elliotmartin92/hv_lock/accurate_models/back_edge_crop.png

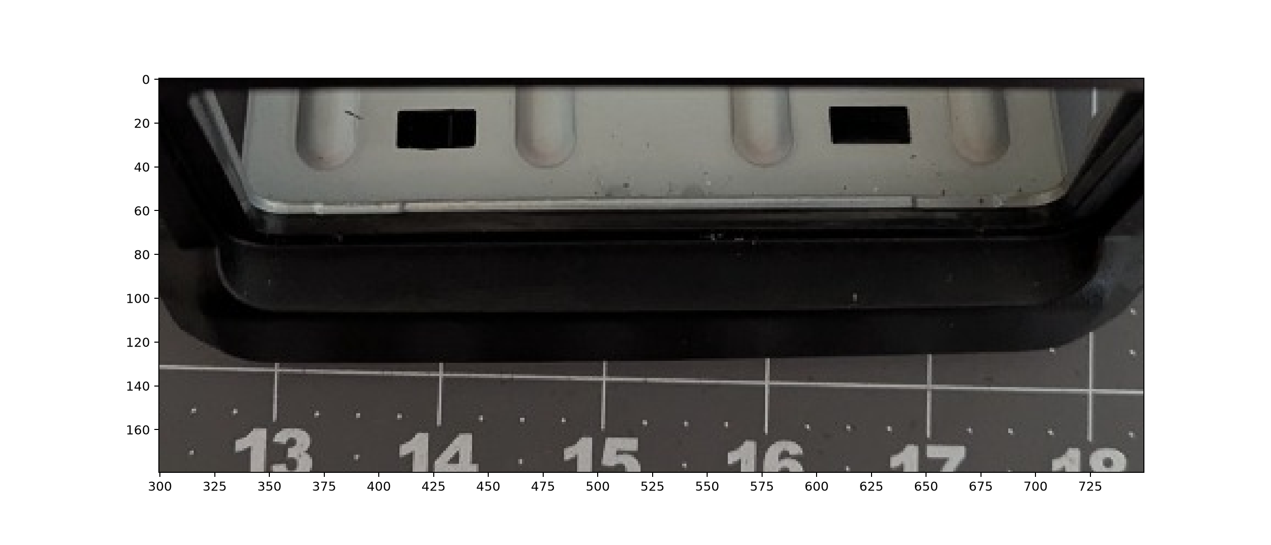
accurate_models/back_edge_crop.png
