elliotmartin92/hv_lock/accurate_models/cavity_floor_annotated.png

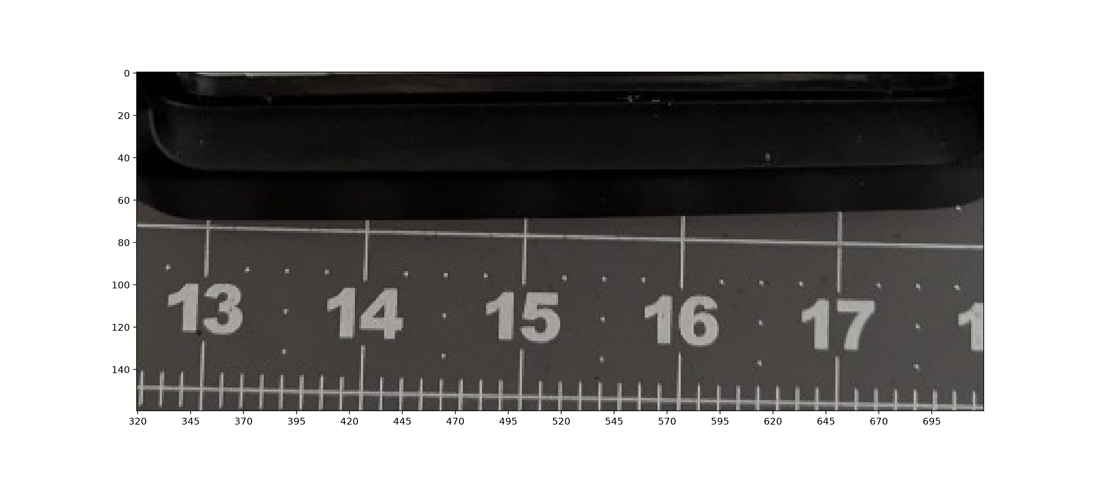
accurate_models/cavity_floor_annotated.png
