elliotmartin92/hv_lock/accurate_models/cavity_zoom.png

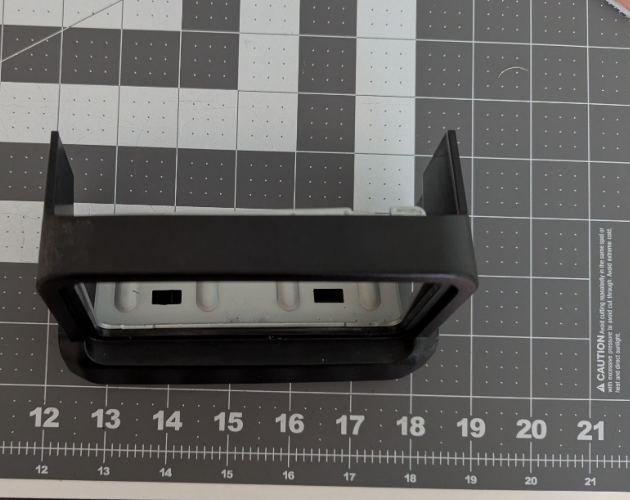
accurate_models/cavity_zoom.png
