elliotmartin92/hv_lock/accurate_models/connector_blueprint.png

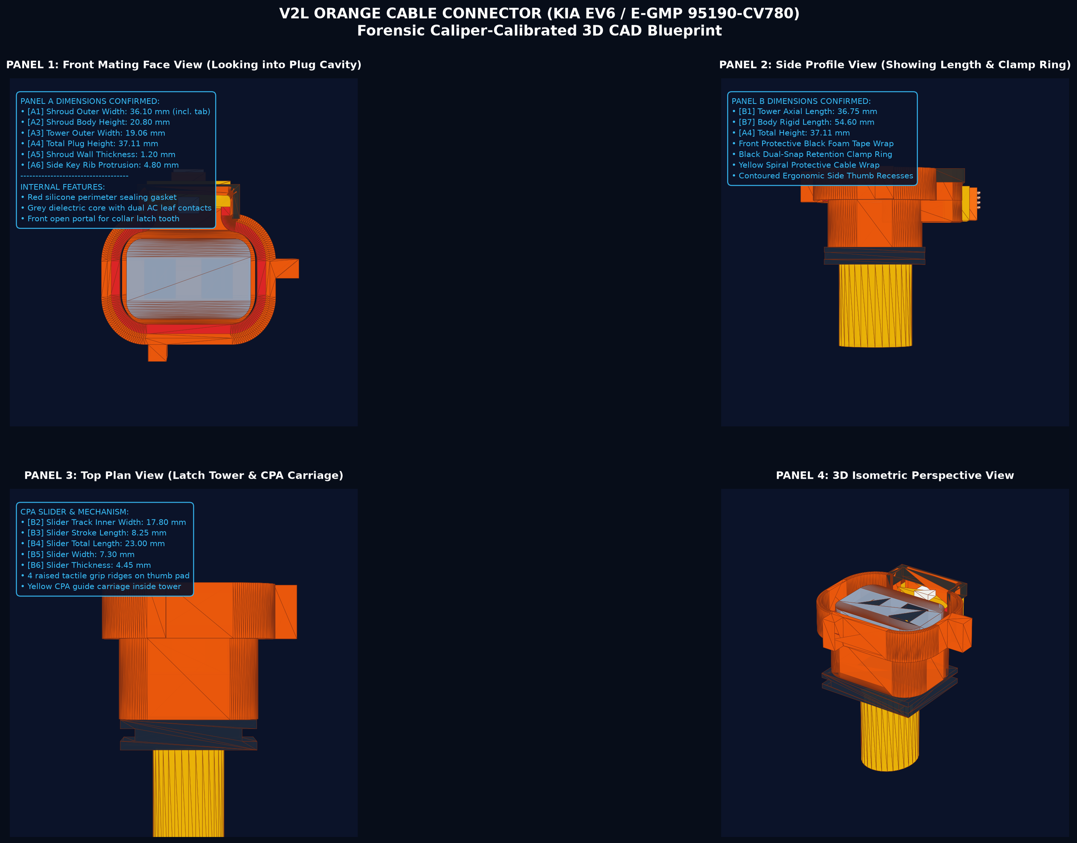
accurate_models/connector_blueprint.png
