elliotmartin92/hv_lock/accurate_models/find_round_holes.png

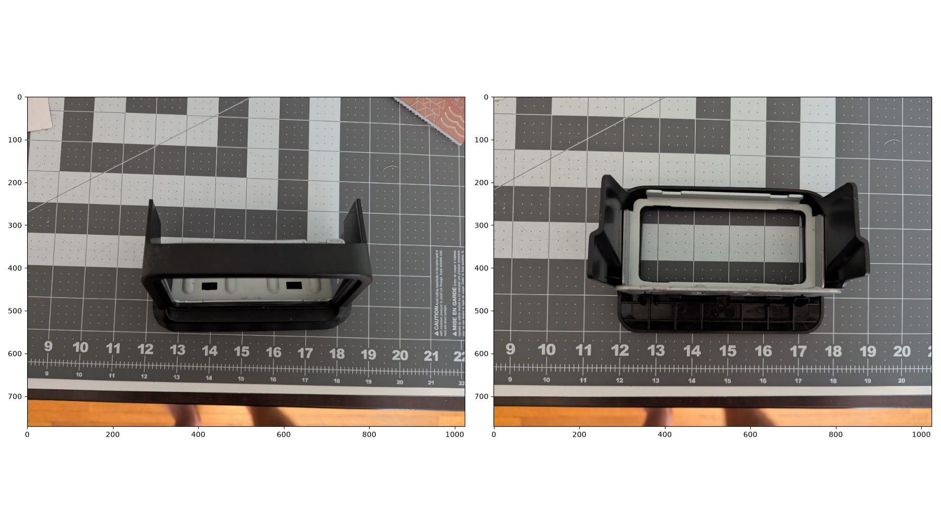
accurate_models/find_round_holes.png
