elliotmartin92/hv_lock/accurate_models/h7_clarification.png

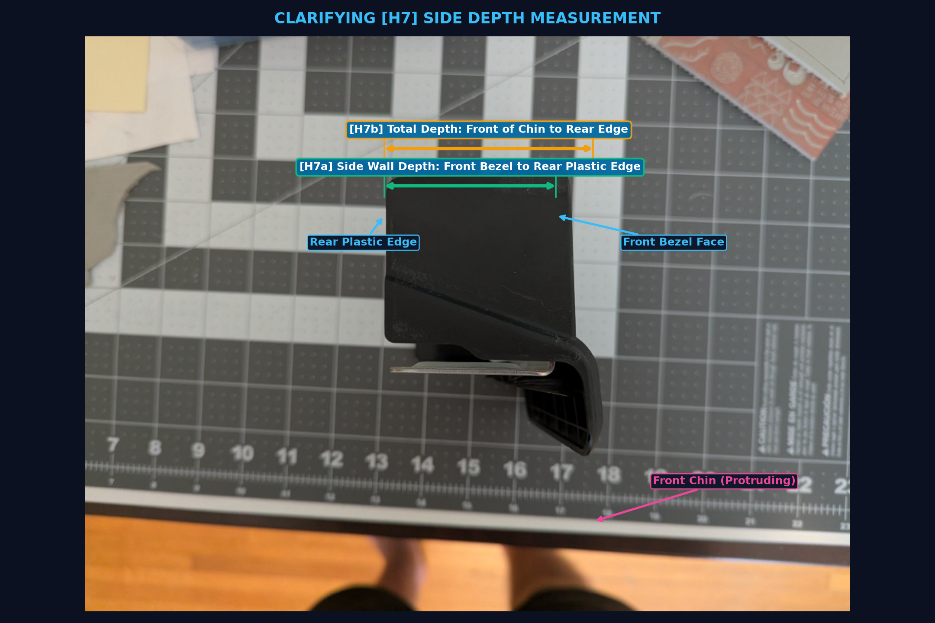
accurate_models/h7_clarification.png
