elliotmartin92/hv_lock/accurate_models/holes_crop.png

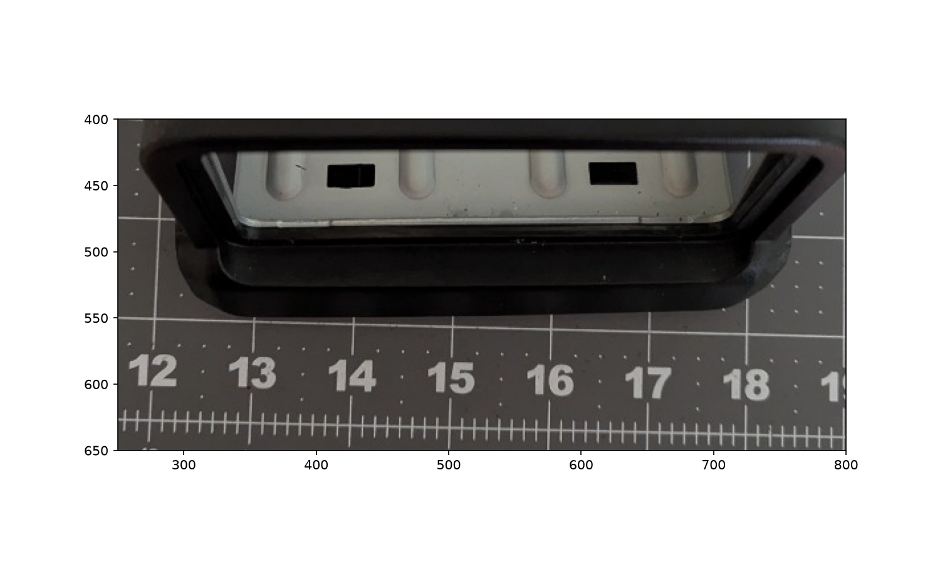
accurate_models/holes_crop.png
