elliotmartin92/hv_lock/accurate_models/holes_zoom.png

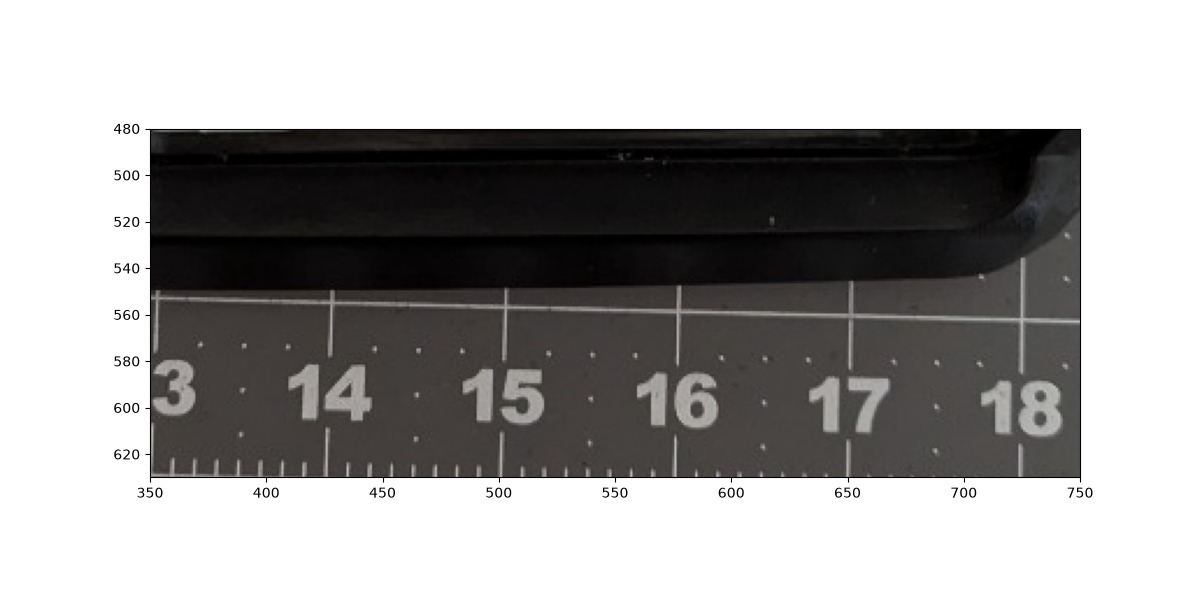
accurate_models/holes_zoom.png
