elliotmartin92/hv_lock/accurate_models/left_vs_right_check.png

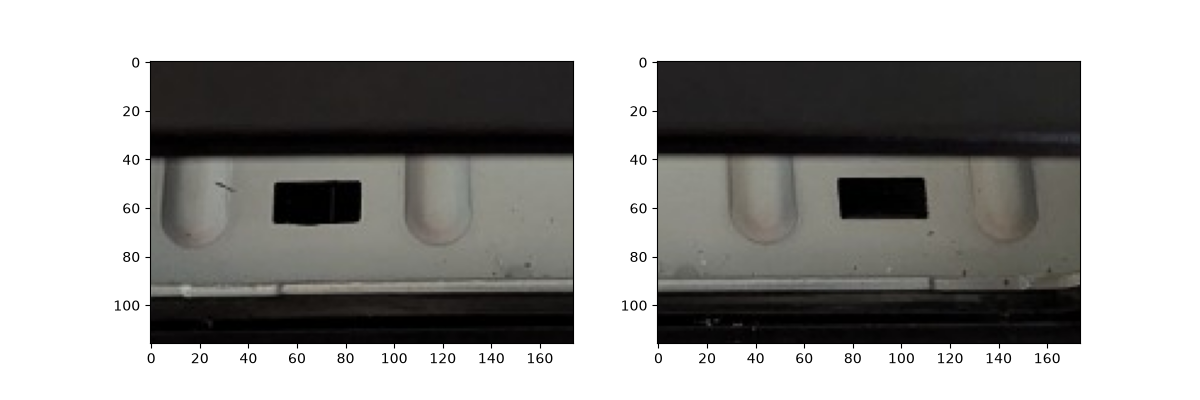
accurate_models/left_vs_right_check.png
