elliotmartin92/hv_lock/accurate_models/outer_housing_blueprint.png

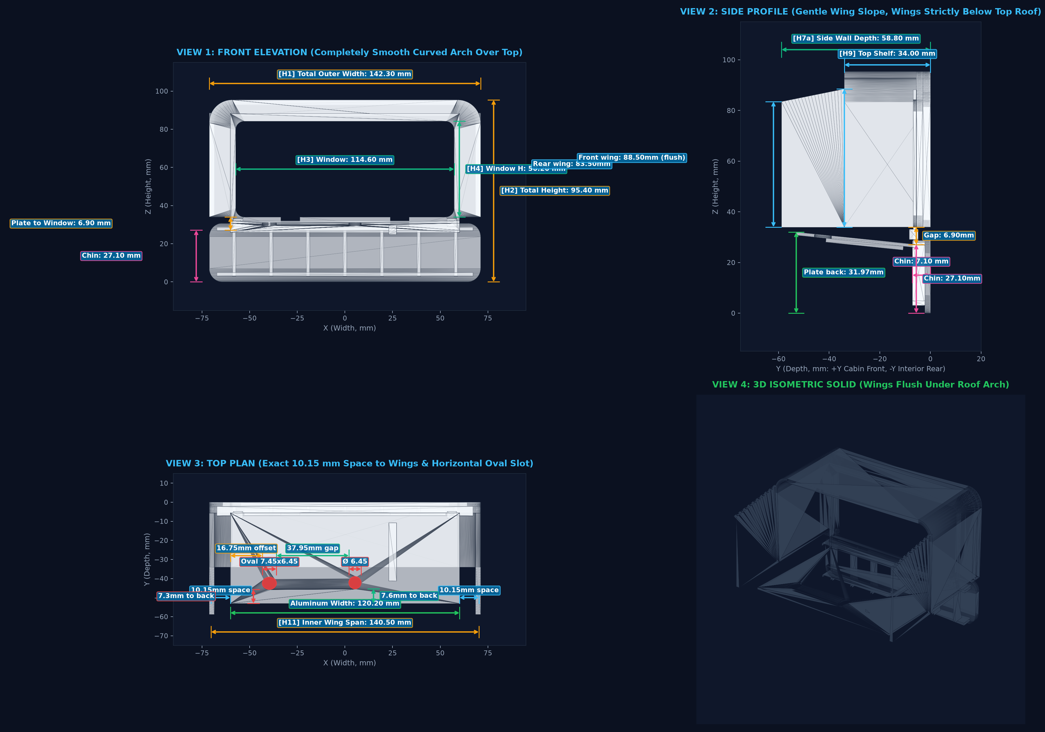
accurate_models/outer_housing_blueprint.png
