elliotmartin92/hv_lock/accurate_models/outlet_box_blueprint.png

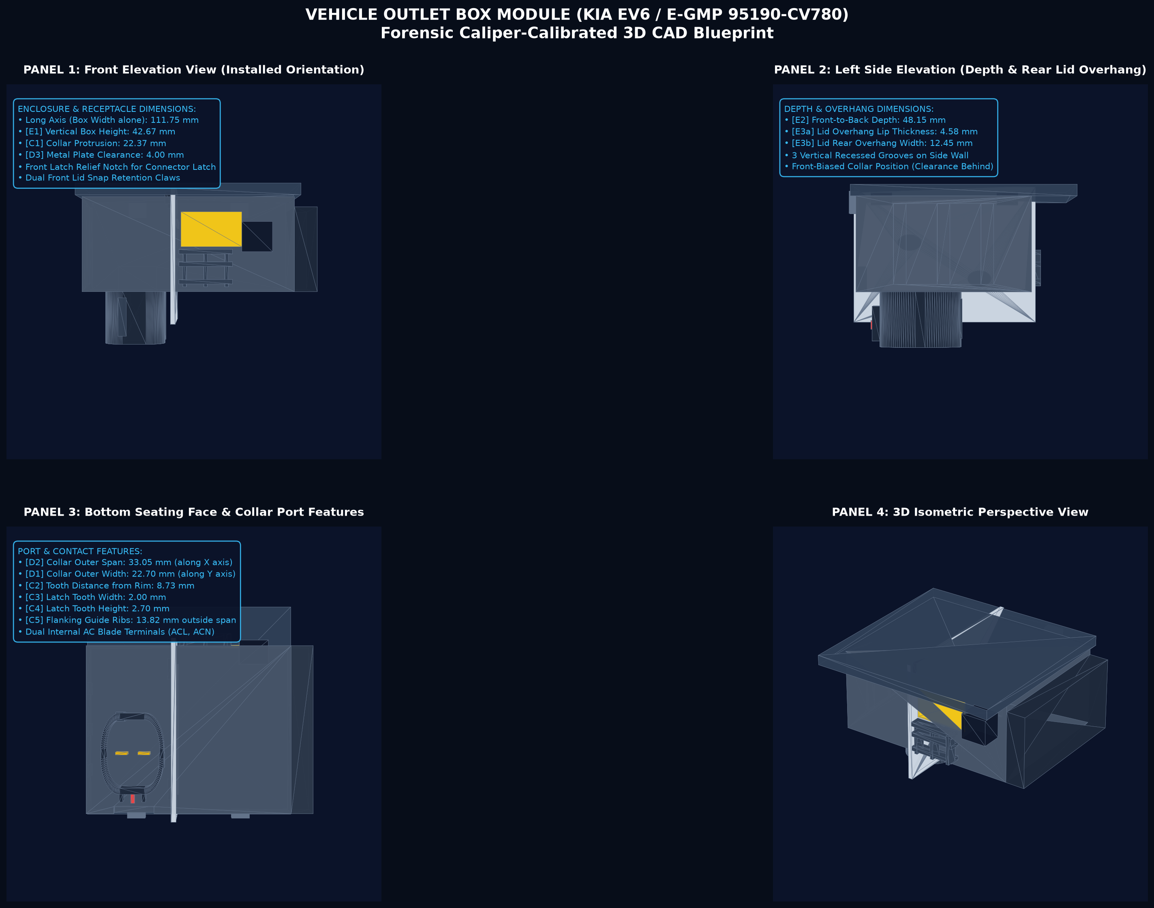
accurate_models/outlet_box_blueprint.png
