elliotmartin92/hv_lock/accurate_models/photo1_zoom.png

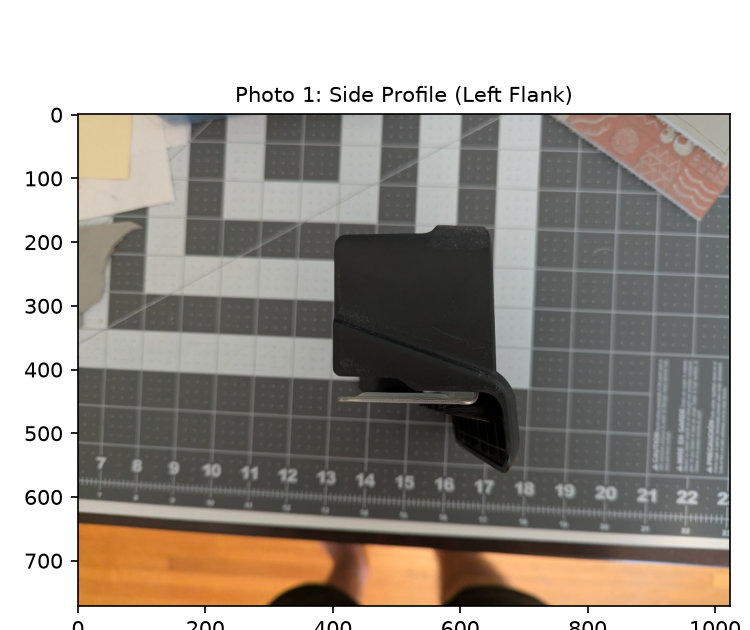
accurate_models/photo1_zoom.png
