elliotmartin92/hv_lock/accurate_models/photo3_zoom.png

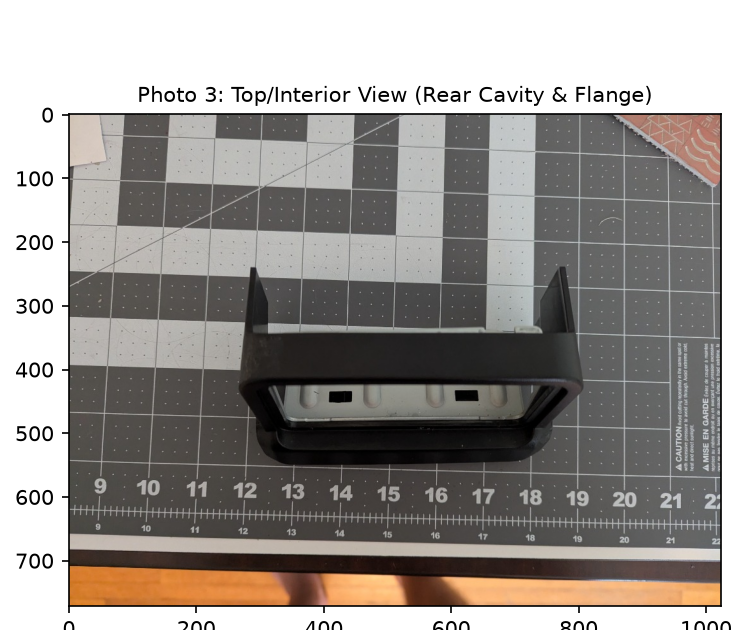
accurate_models/photo3_zoom.png
