elliotmartin92/hv_lock/accurate_models/photo5_zoom.png

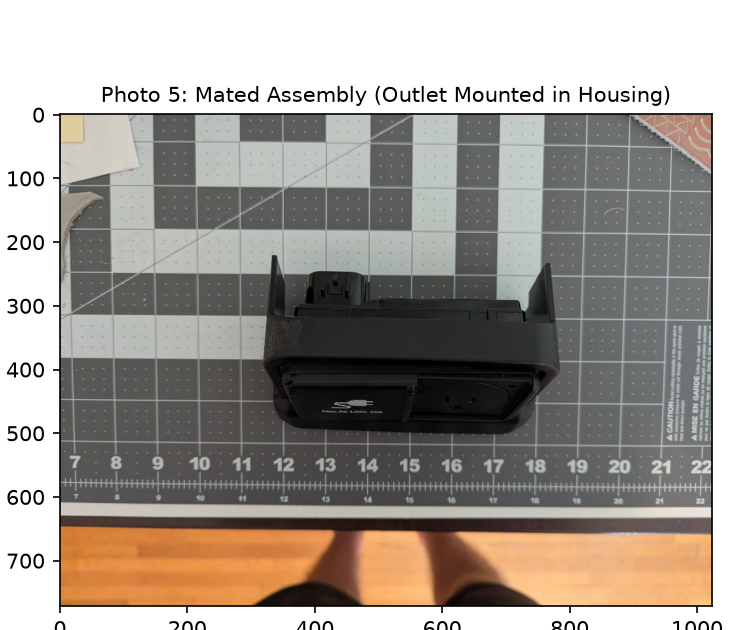
accurate_models/photo5_zoom.png
