elliotmartin92/hv_lock/accurate_models/plate_angle_lines.png

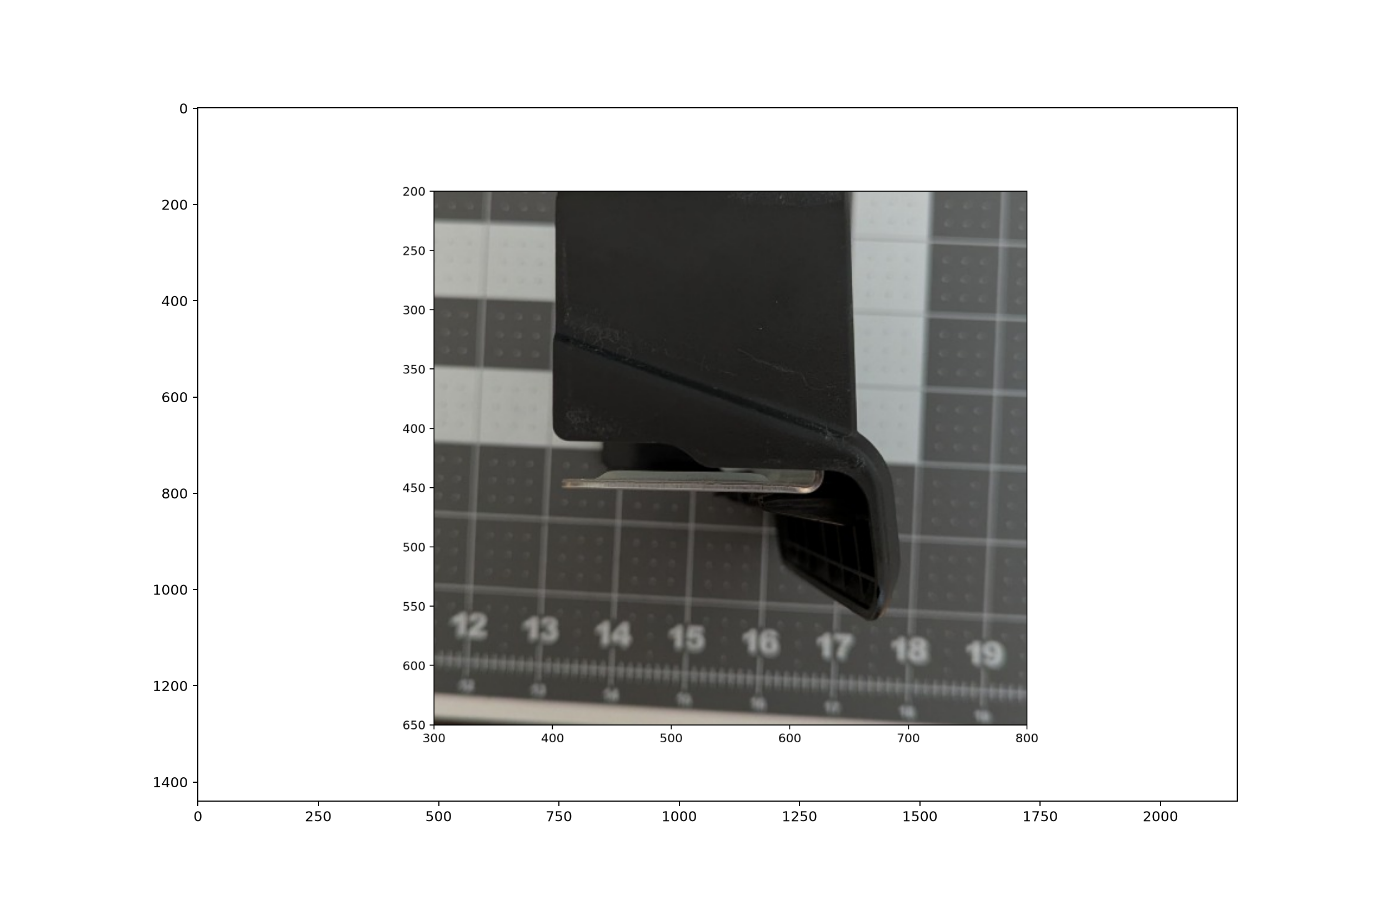
accurate_models/plate_angle_lines.png
