elliotmartin92/hv_lock/accurate_models/plate_angle_study.png

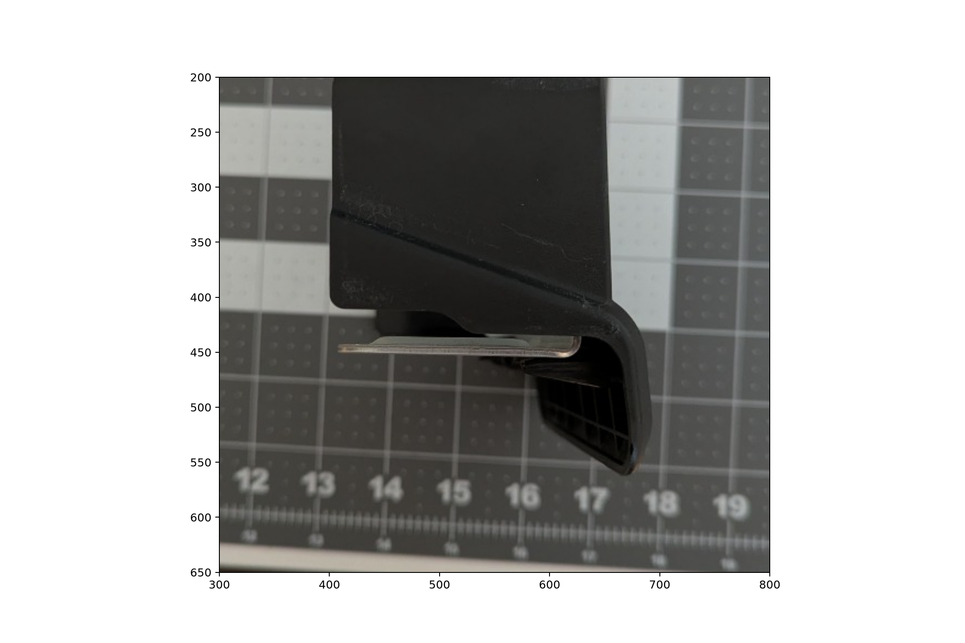
accurate_models/plate_angle_study.png
