elliotmartin92/hv_lock/accurate_models/profile_study.png

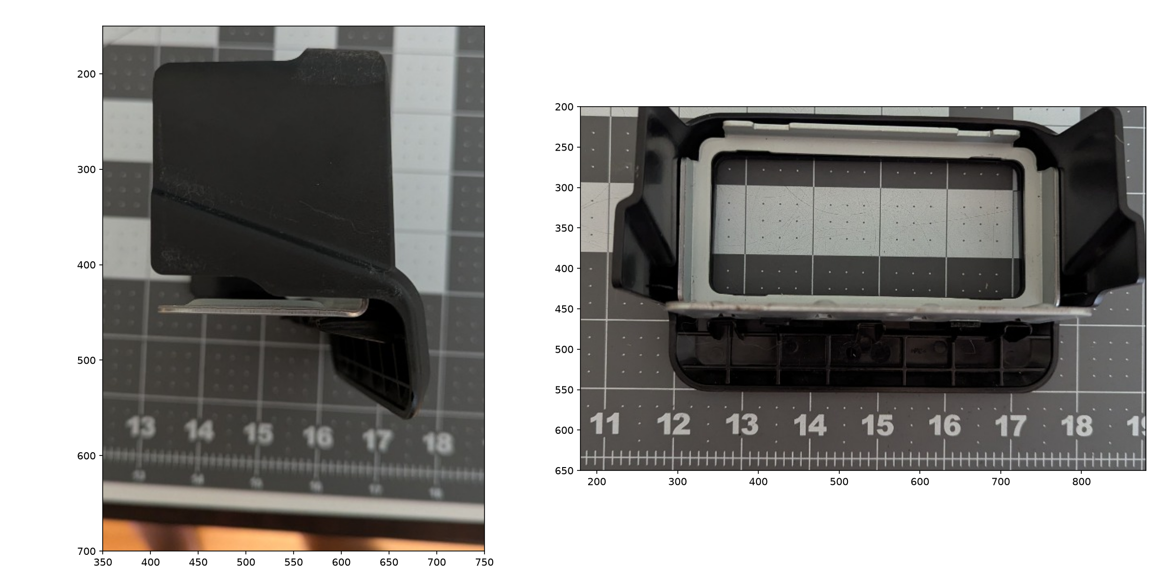
accurate_models/profile_study.png
