elliotmartin92/hv_lock/accurate_models/rear_plate_zoom.png

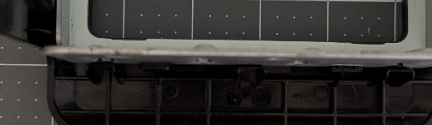
accurate_models/rear_plate_zoom.png
