elliotmartin92/hv_lock/accurate_models/rear_zoom.png

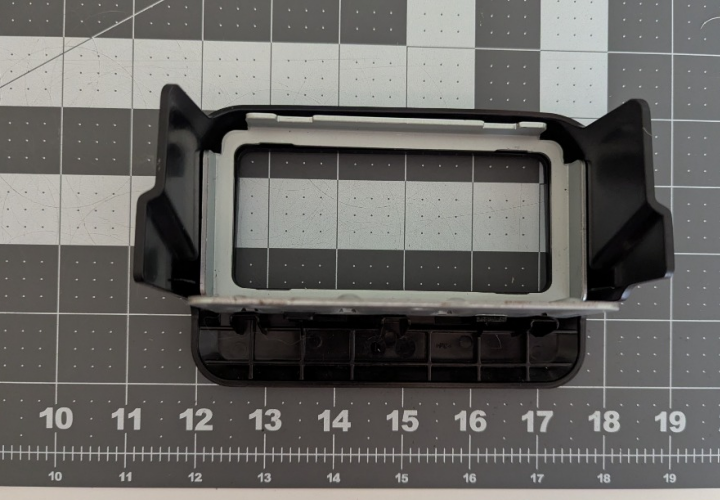
accurate_models/rear_zoom.png
