elliotmartin92/hv_lock/accurate_models/ruler_crop.png

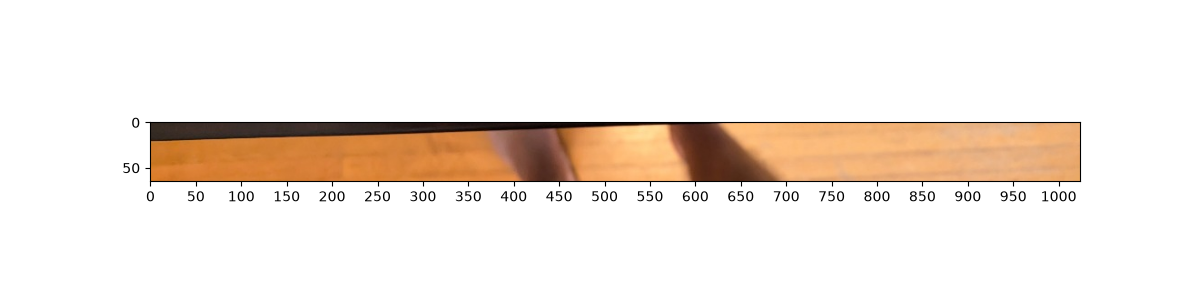
accurate_models/ruler_crop.png
