elliotmartin92/hv_lock/accurate_models/wing_bottom_check.png

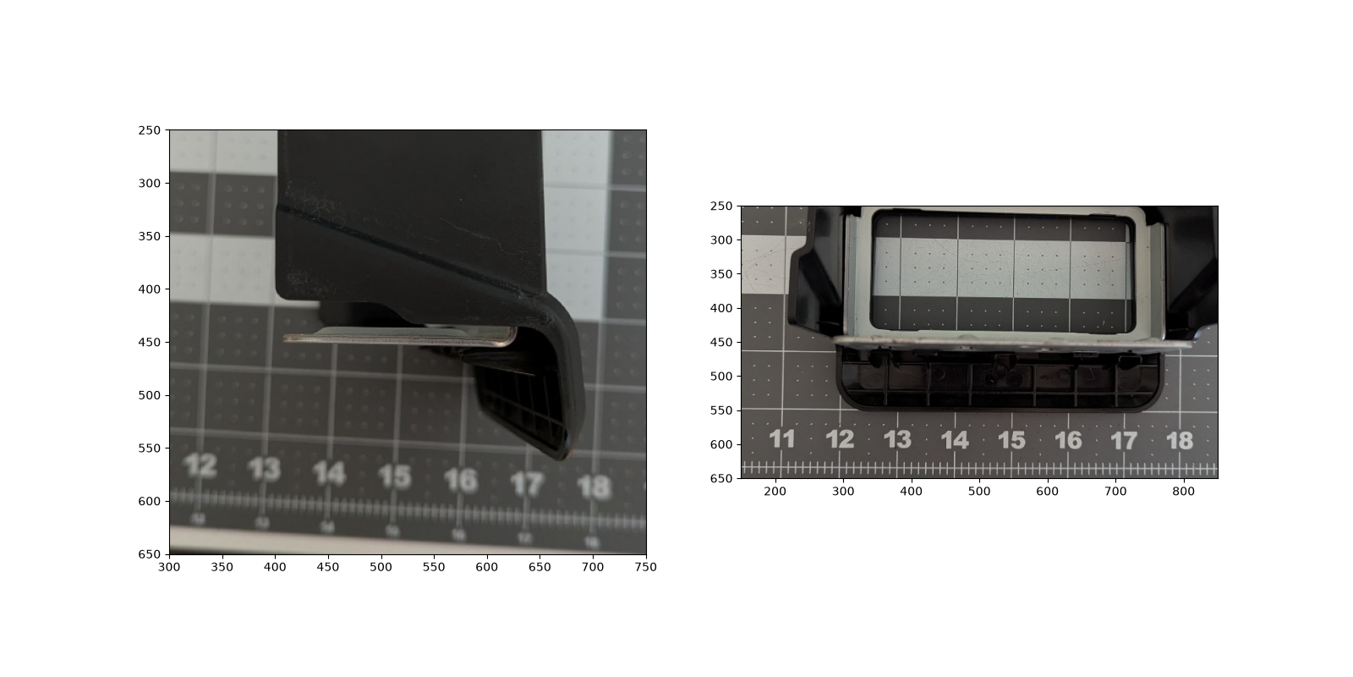
accurate_models/wing_bottom_check.png
