elliotmartin92/hv_lock/accurate_models/wing_slope_study.png

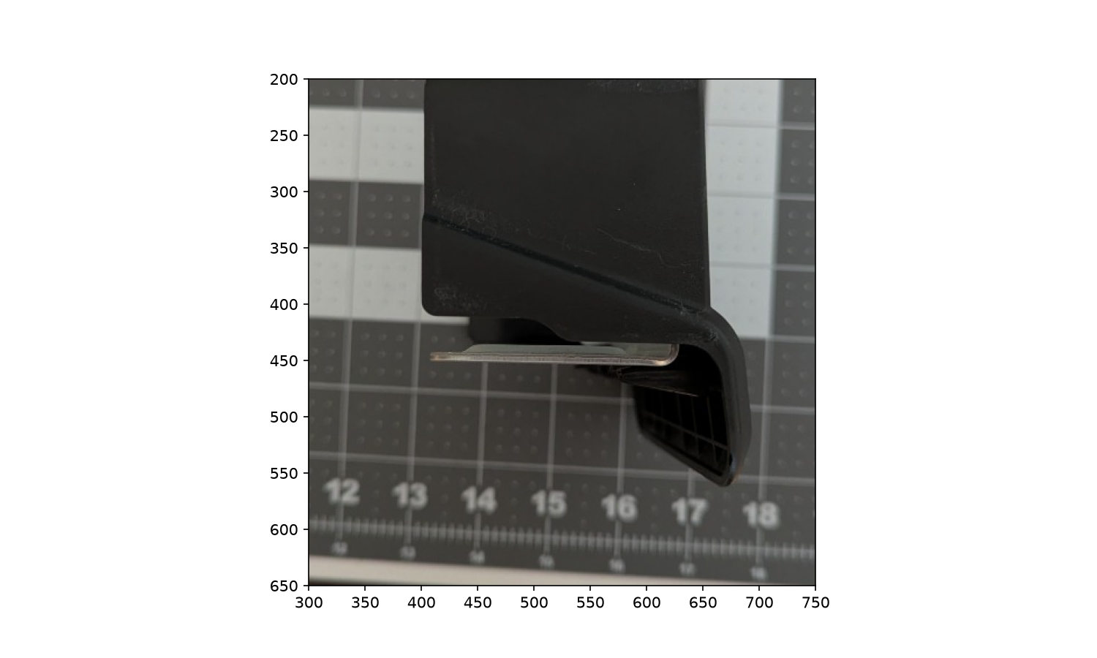
accurate_models/wing_slope_study.png
