elliotmartin92/hv_lock/lock_v2/cradle_floor_ortho_comparison.png

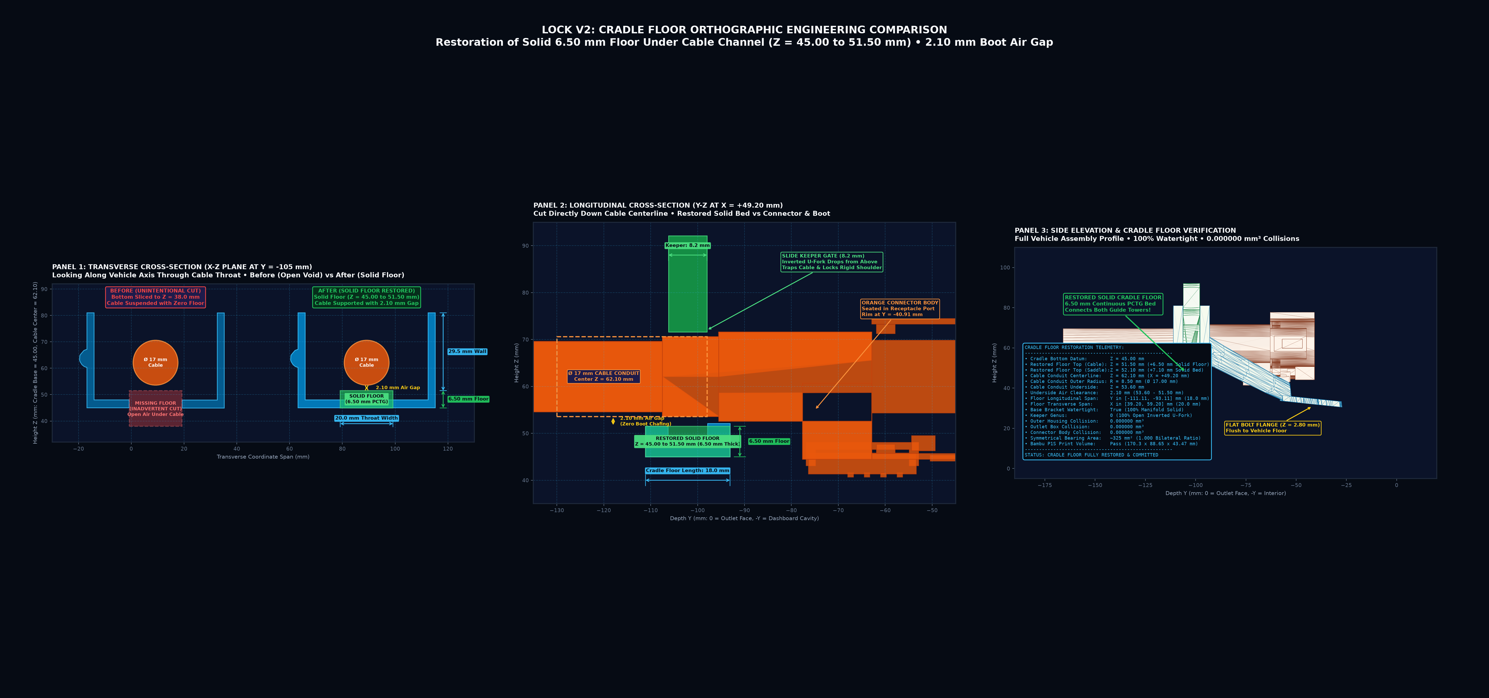
lock_v2/cradle_floor_ortho_comparison.png
