elliotmartin92/hv_lock/lock_v2/lock_v2_blueprint.png

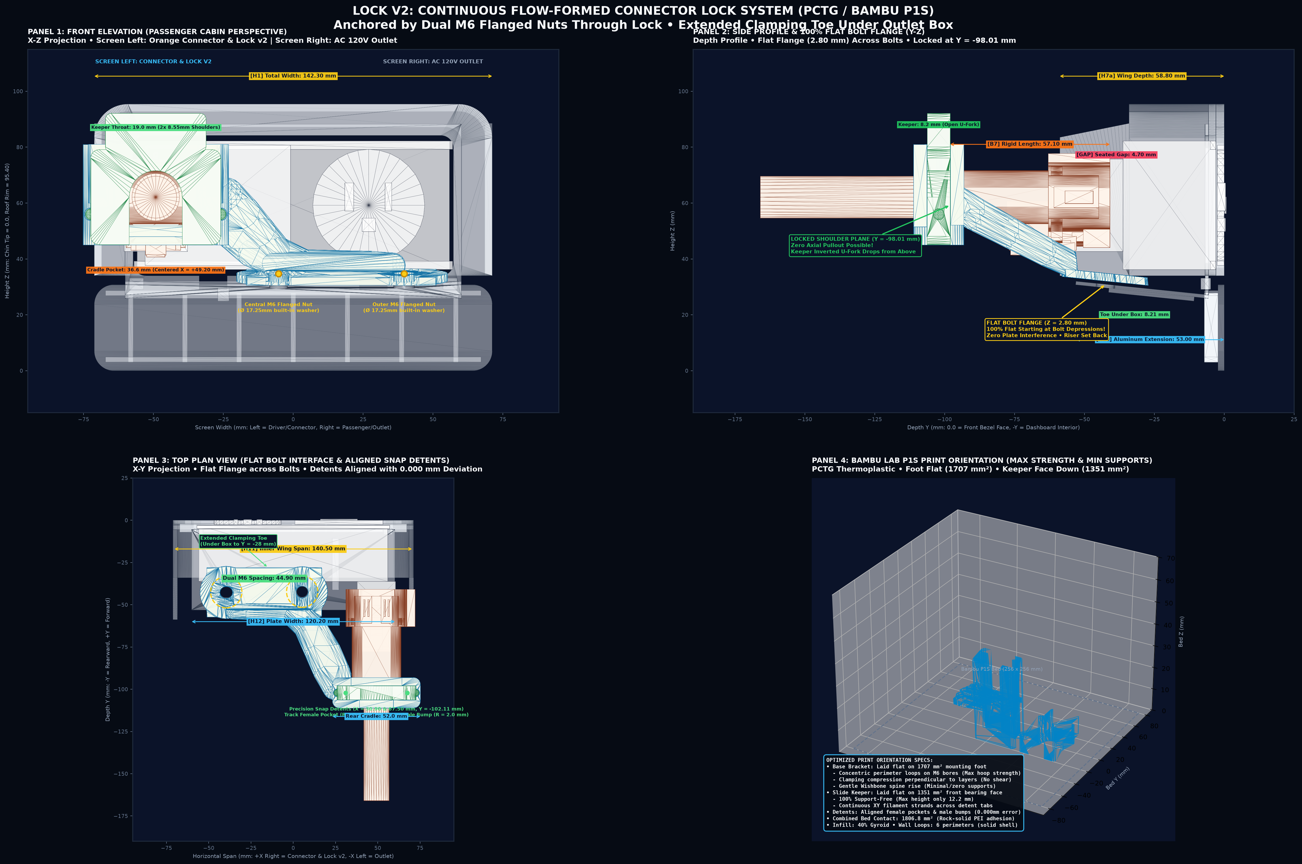
lock_v2/lock_v2_blueprint.png
