elliotmartin92/hv_lock/lock_v2/ortho_top_down_comparison.png

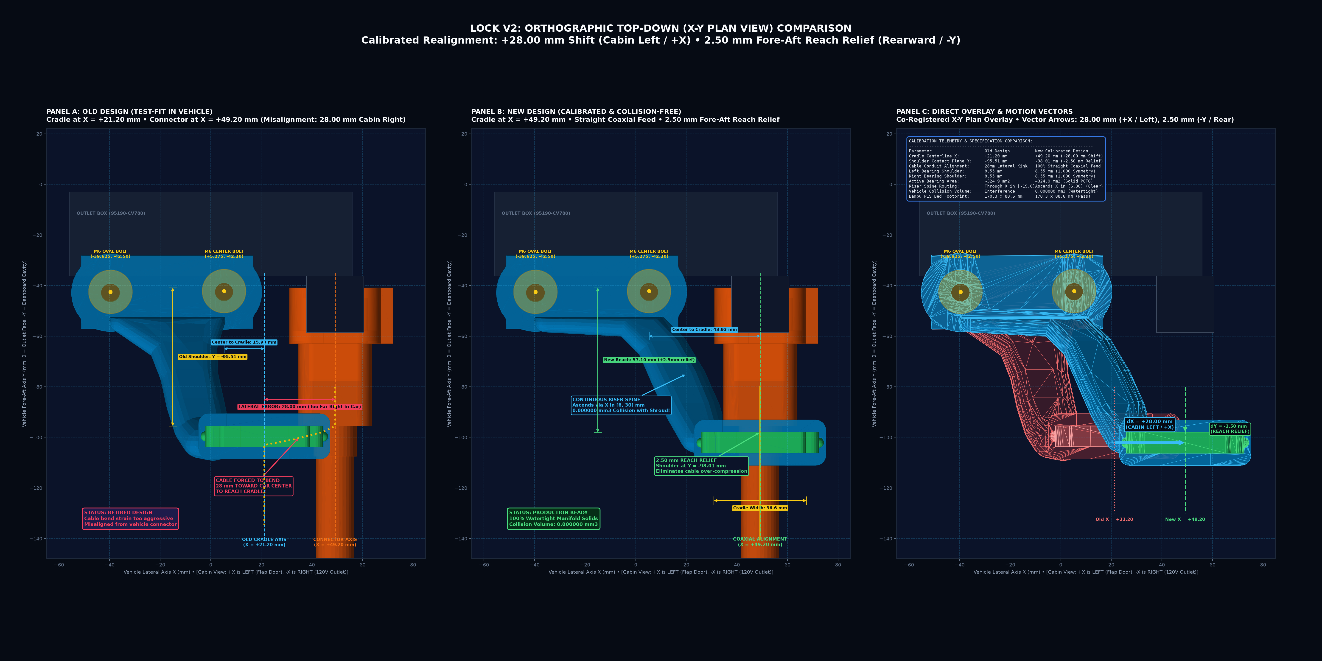
lock_v2/ortho_top_down_comparison.png
