elliotmartin92/hv_lock/testing/chassis_bolt_lock_v2.png

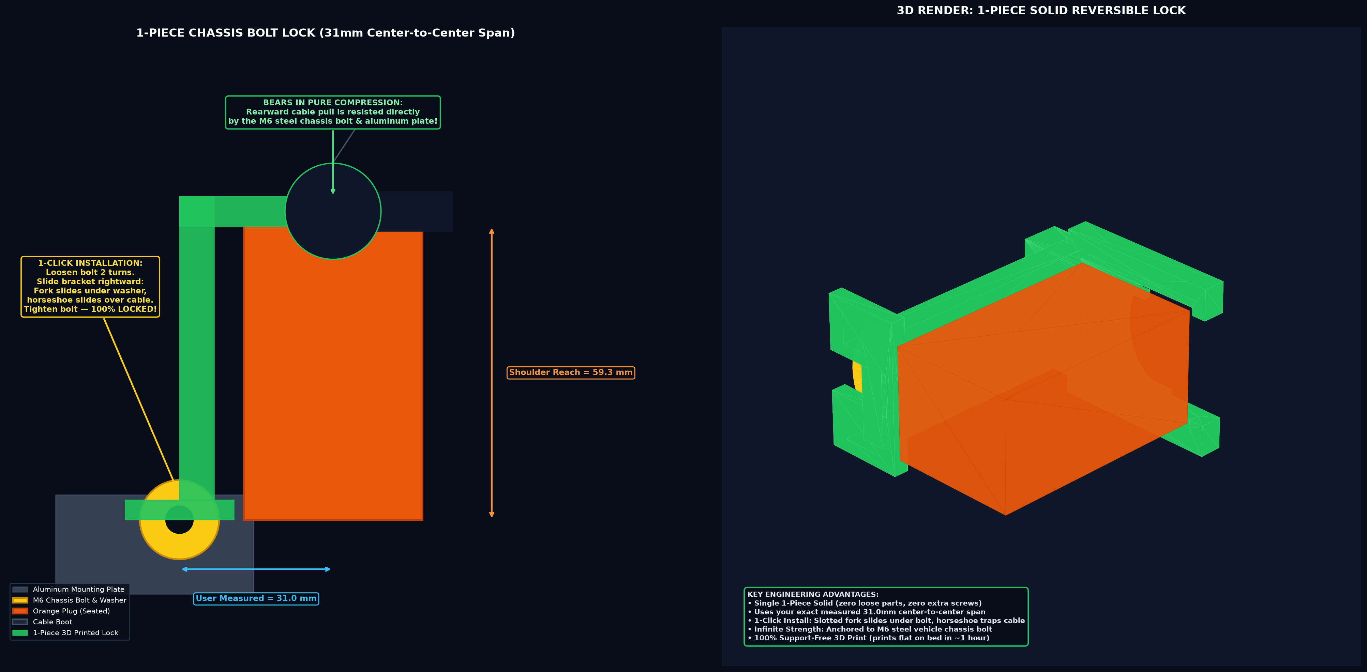
testing/chassis_bolt_lock_v2.png
