elliotmartin92/hv_lock/testing/three_concepts_illustrated.png

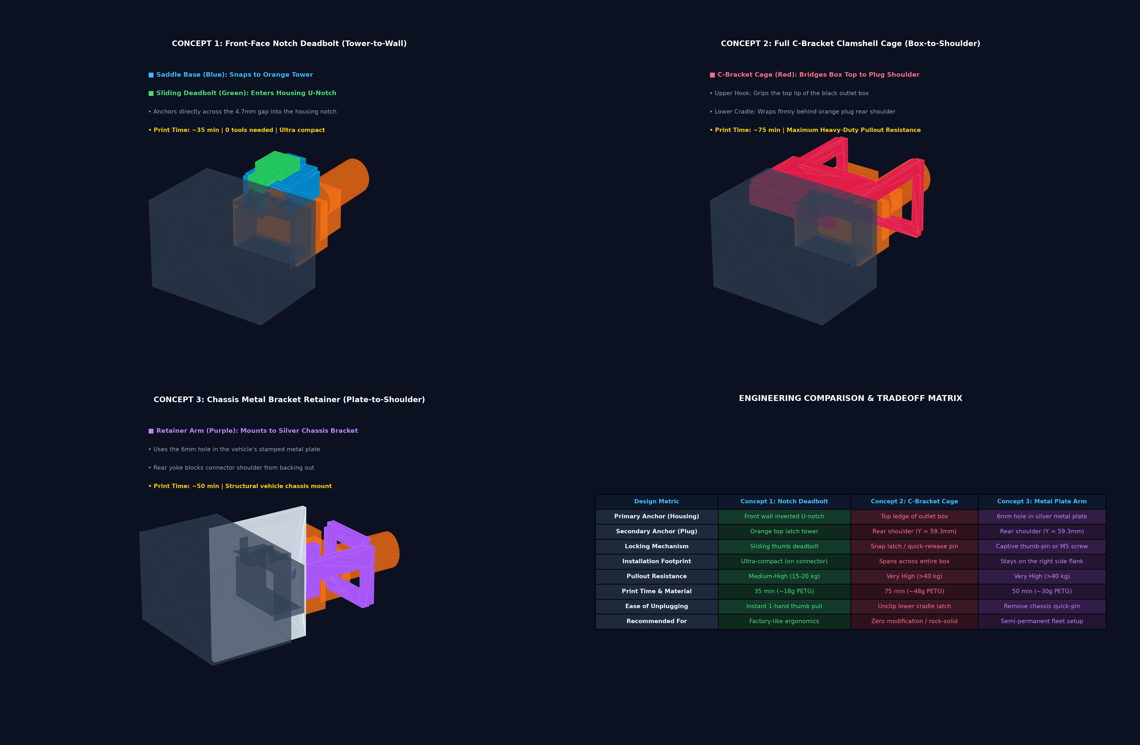
testing/three_concepts_illustrated.png
