elliotmartin92/hv_lock/lock_v2/lock_v2_base_bracket_blown_floor.stl

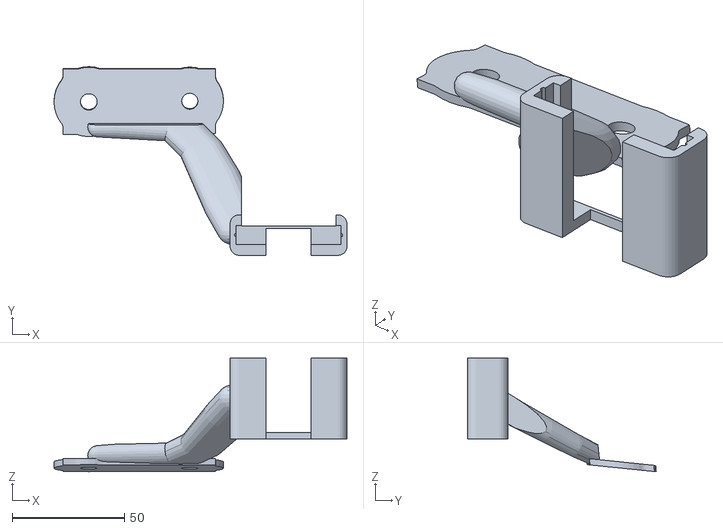
[picture p47: CAD file, 2026-09-19]
lock_v2/lock_v2_base_bracket_blown_floor.stl
130.3 x 83.9 x 50.5
