elliotmartin92/hv_lock/accurate_models/outlet_box_model.stl

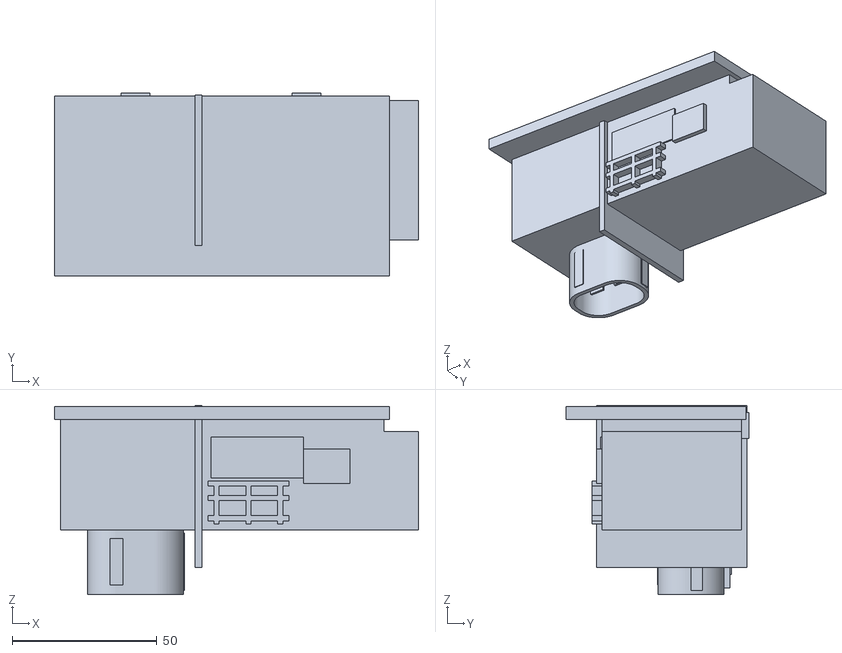
[picture p48: CAD file, 2026-09-03]
accurate_models/outlet_box_model.stl
125.8 x 63.1 x 65.4
