elliotmartin92/hv_lock/lock_v2/lock_v2_keeper.stl

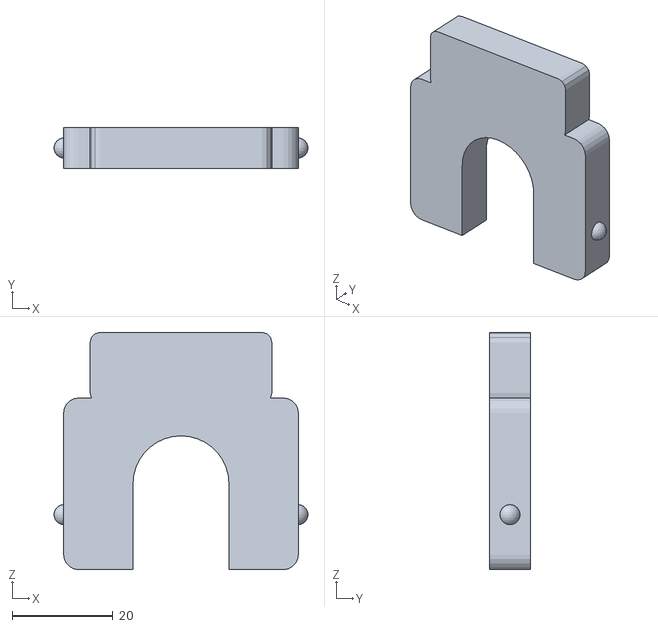
[picture p49: CAD file, 2026-09-19]
lock_v2/lock_v2_keeper.stl
50.3 x 8.20 x 47.0
