elliotmartin92/hv_lock/testing/concept2_c_bracket_cage.stl

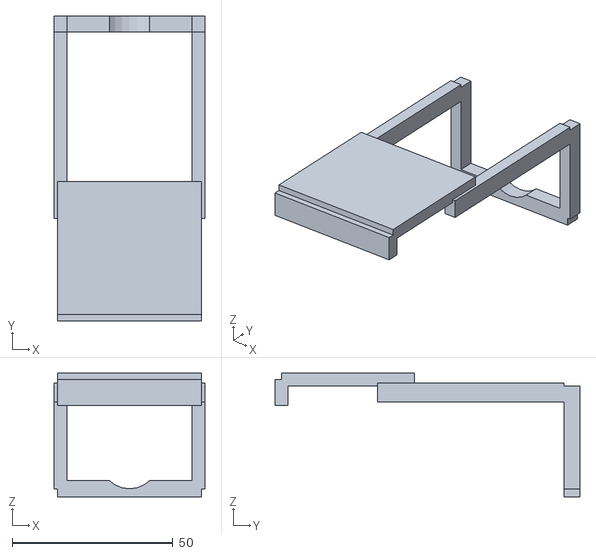
[picture p50: CAD file, 2026-09-03]
testing/concept2_c_bracket_cage.stl
47.0 x 95.0 x 38.5
