elliotmartin92/hv_lock/testing/c_bracket_keeper.stl

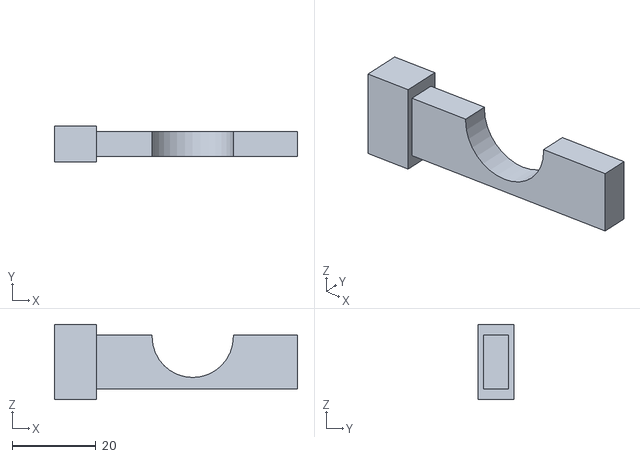
[picture p51: CAD file, 2026-09-03]
testing/c_bracket_keeper.stl
58.1 x 8.50 x 18.0
