elliotmartin92/hv_lock/testing/seated_housing.stl

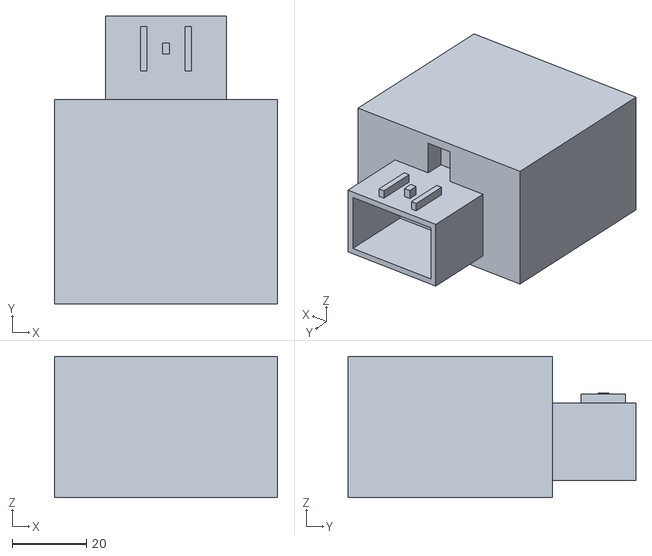
[picture p52: CAD file, 2026-09-03]
testing/seated_housing.stl
60.0 x 77.4 x 38.0
