elliotmartin92/hv_lock/testing/print_plate_all_parts.stl

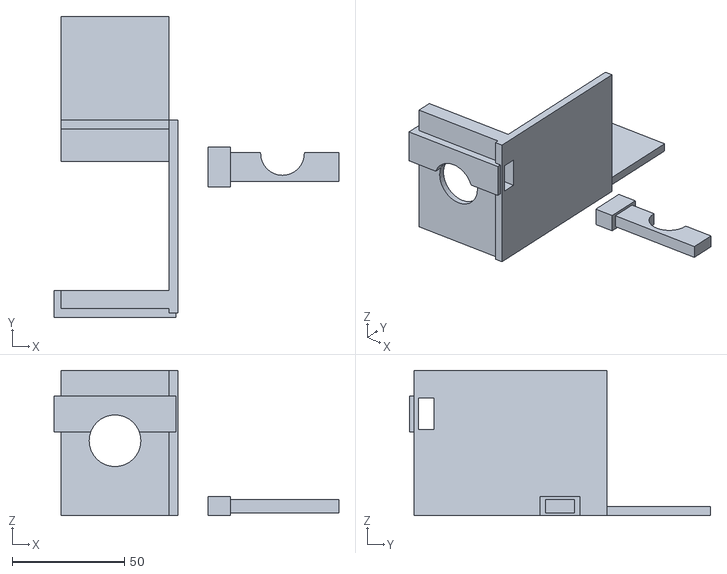
[picture p53: CAD file, 2026-09-03]
testing/print_plate_all_parts.stl
126.6 x 133.9 x 64.7
