elliotmartin92/hv_lock/testing/hv_lock_slider.stl

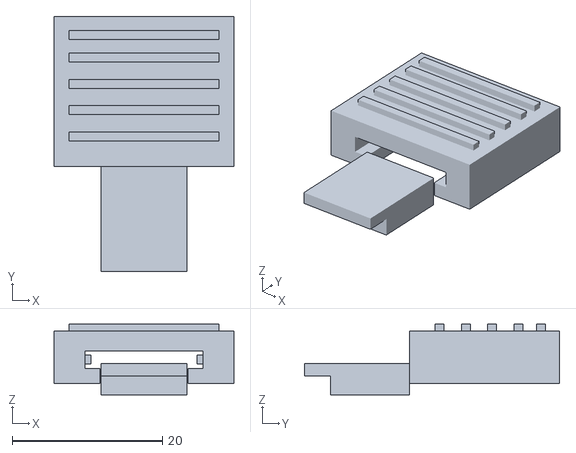
[picture p54: CAD file, 2026-09-03]
testing/hv_lock_slider.stl
24.0 x 34.0 x 9.40
