elliotmartin92/hv_lock/testing/c_bracket_spine.stl

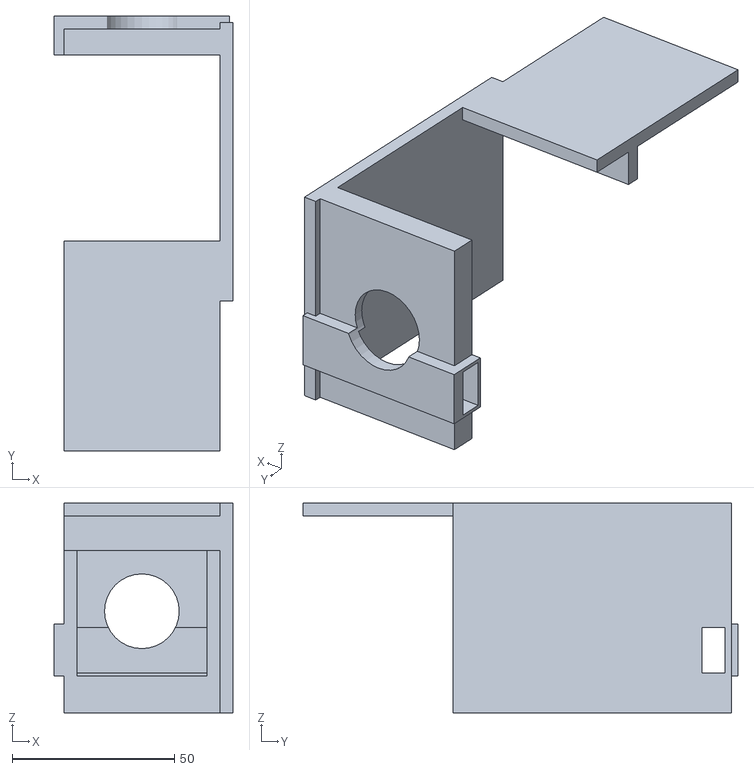
[picture p55: CAD file, 2026-09-03]
testing/c_bracket_spine.stl
55.1 x 133.9 x 64.7
