elliotmartin92/hv_lock/testing/context_plug.obj

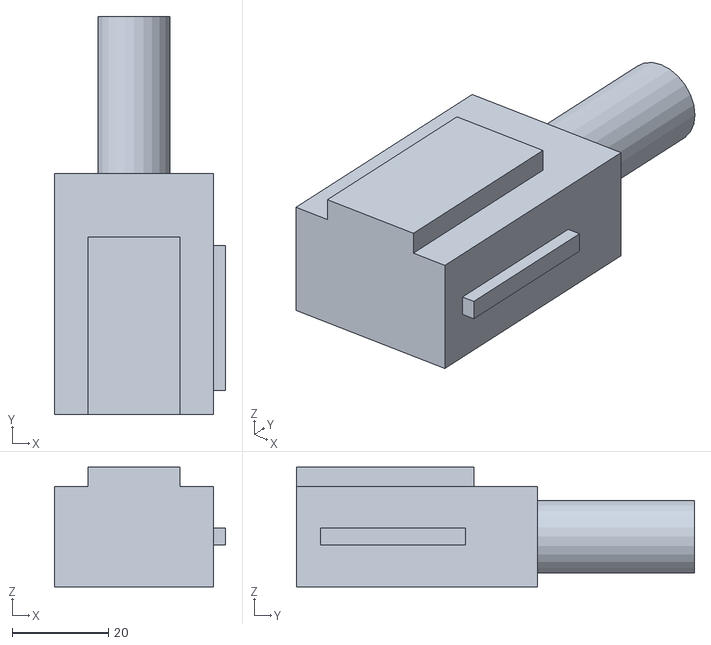
[picture p56: CAD file, 2026-09-03]
testing/context_plug.obj
35.5 x 82.5 x 24.8
