elliotmartin92/hv_lock/testing/option2_bridle.stl

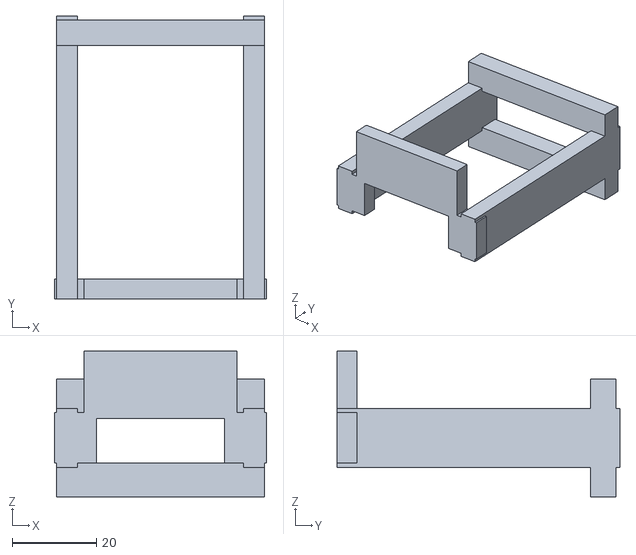
[picture p57: CAD file, 2026-09-03]
testing/option2_bridle.stl
50.5 x 67.3 x 34.6
