elliotmartin92/hv_lock/testing/option2_clamp_jaw.stl

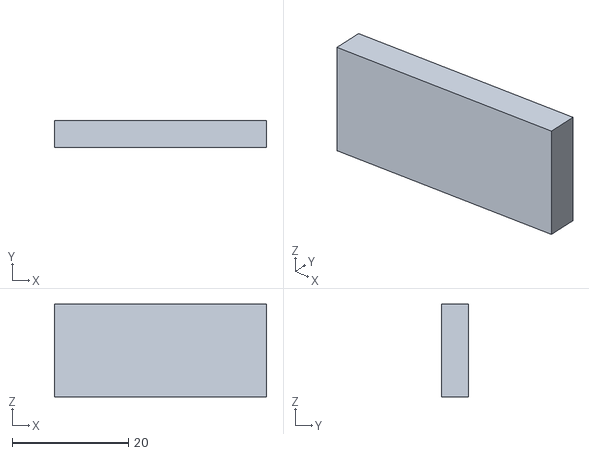
[picture p58: CAD file, 2026-09-03]
testing/option2_clamp_jaw.stl
36.5 x 4.70 x 16.0
