elliotmartin92/hv_lock/testing/context_bracket.obj

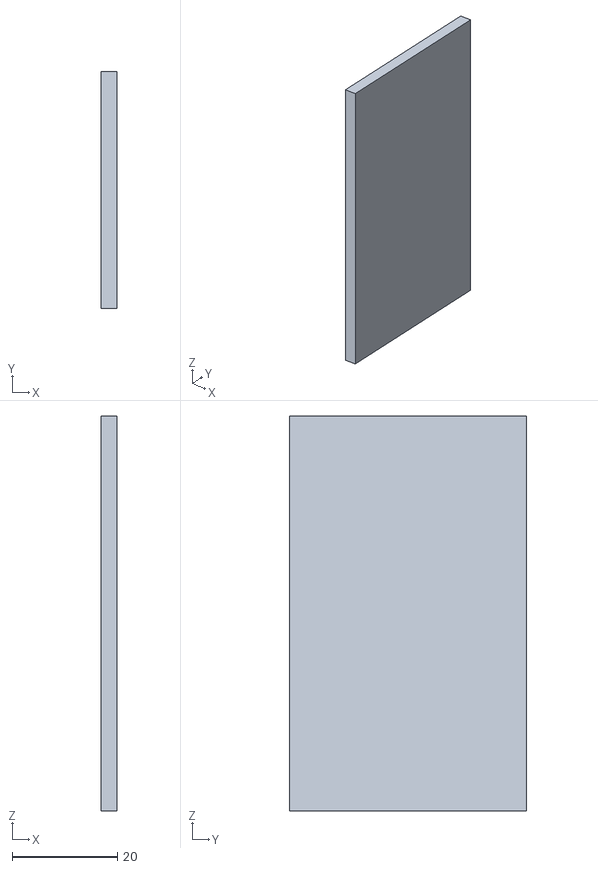
[picture p59: CAD file, 2026-09-03]
testing/context_bracket.obj
3.00 x 45.0 x 75.0
