elliotmartin92/hv_lock/testing/c_bracket_plate.stl

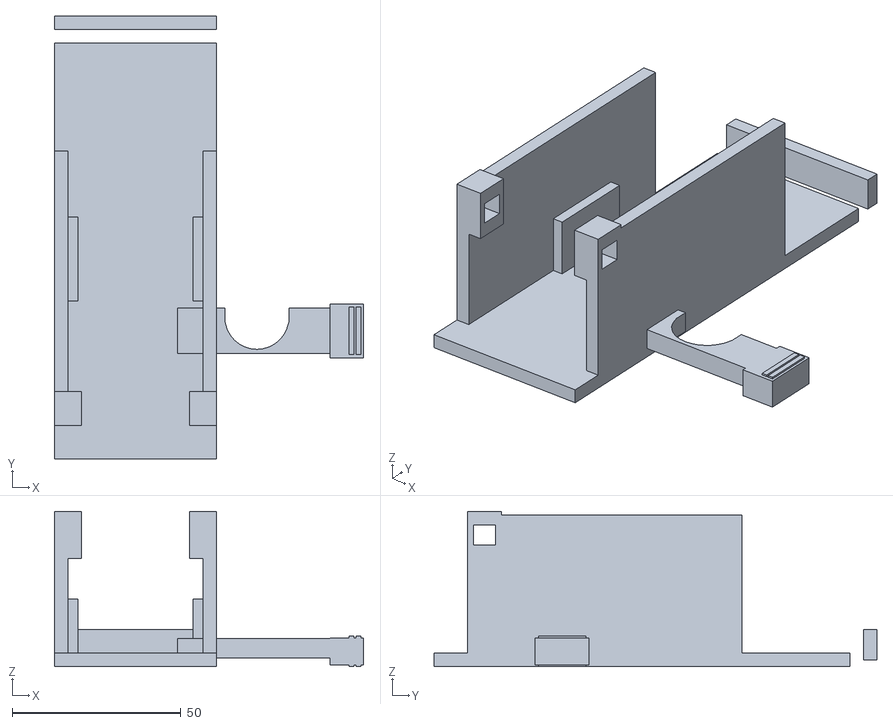
[picture p60: CAD file, 2026-09-03]
testing/c_bracket_plate.stl
91.6 x 131.3 x 46.0
