elliotmartin92/hv_lock/testing/hv_lock_saddle.stl

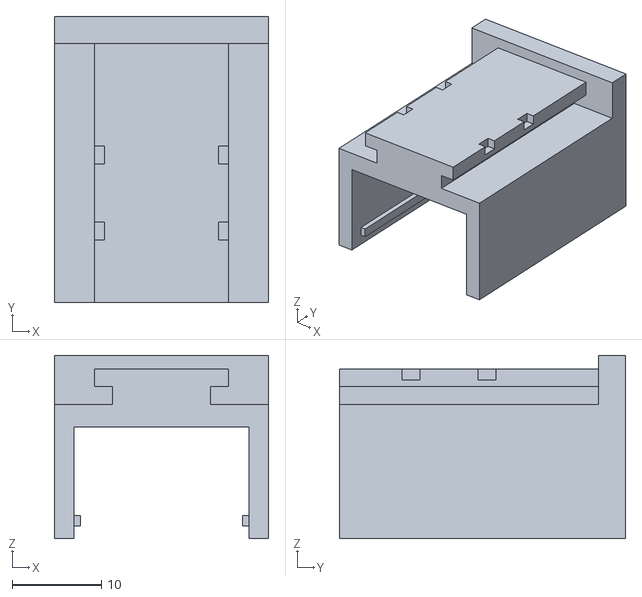
[picture p61: CAD file, 2026-09-03]
testing/hv_lock_saddle.stl
24.0 x 32.0 x 20.5
