elliotmartin92/hv_lock/testing/seated_bracket.stl

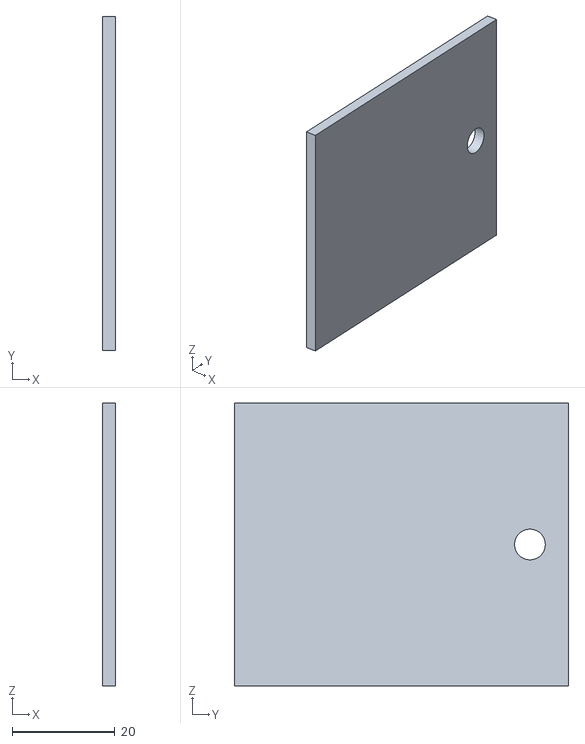
[picture p62: CAD file, 2026-09-03]
testing/seated_bracket.stl
2.50 x 65.0 x 55.0
