elliotmartin92/hv_lock/accurate_models/housing_measuring_guide.png

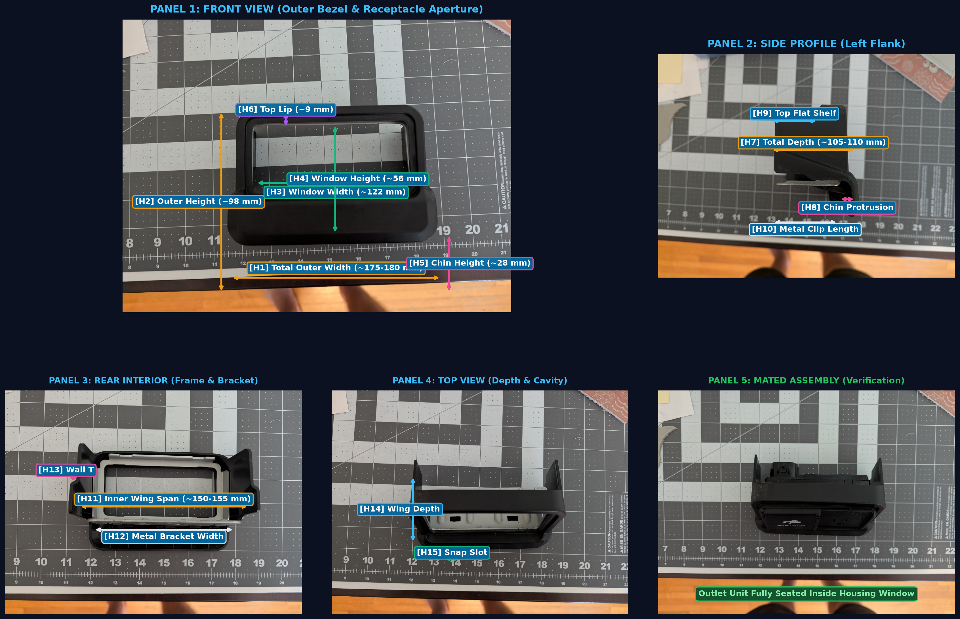
accurate_models/housing_measuring_guide.png
