elliotmartin92/hv_lock/accurate_models/mated_assembly_blueprint_ai.png

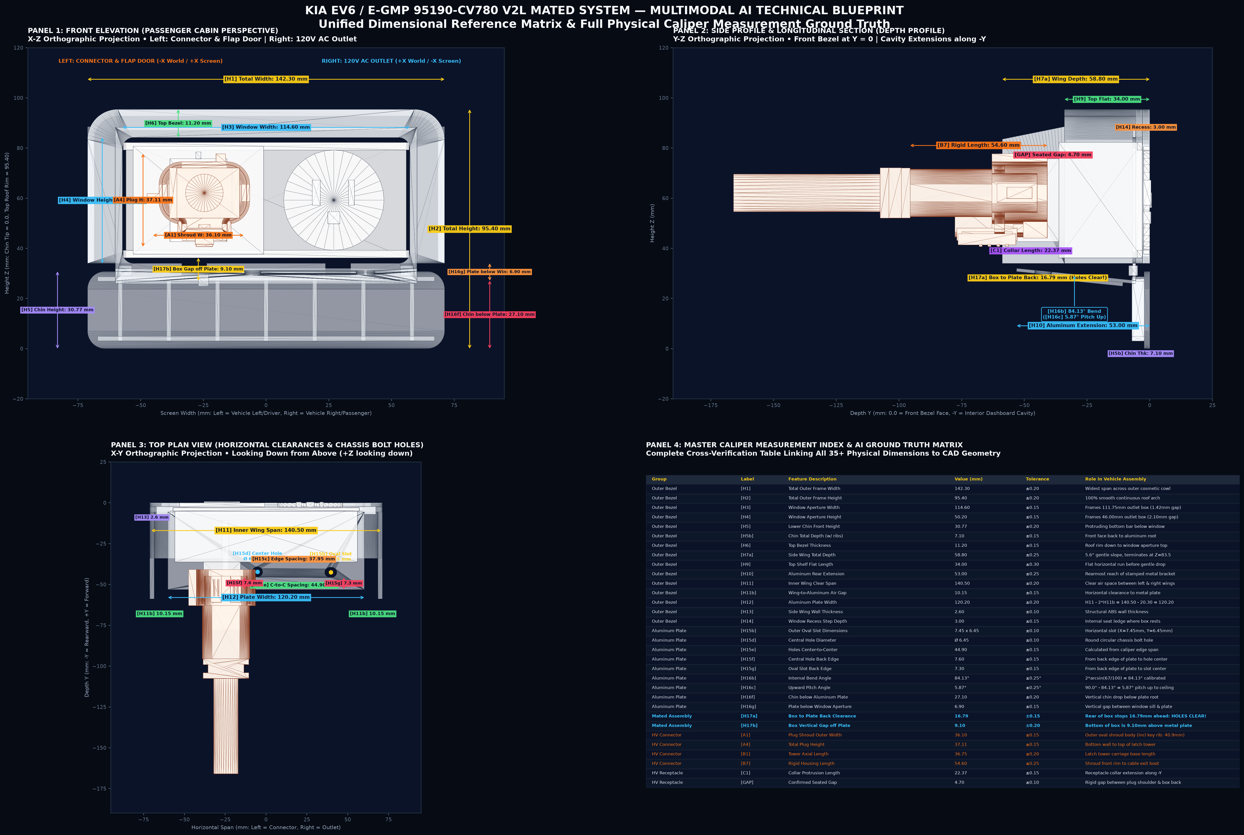
accurate_models/mated_assembly_blueprint_ai.png
