elliotmartin92/hv_lock/testing/box_measuring_guide.png

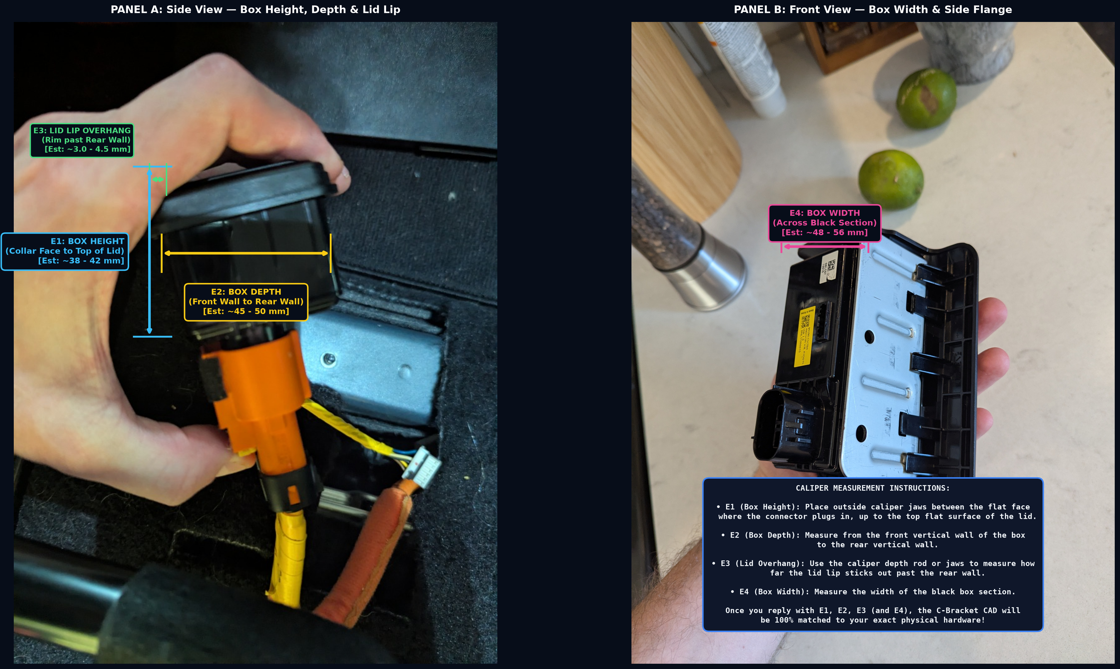
testing/box_measuring_guide.png
