elliotmartin92/hv_lock/testing/seated_assembly_blueprint.png

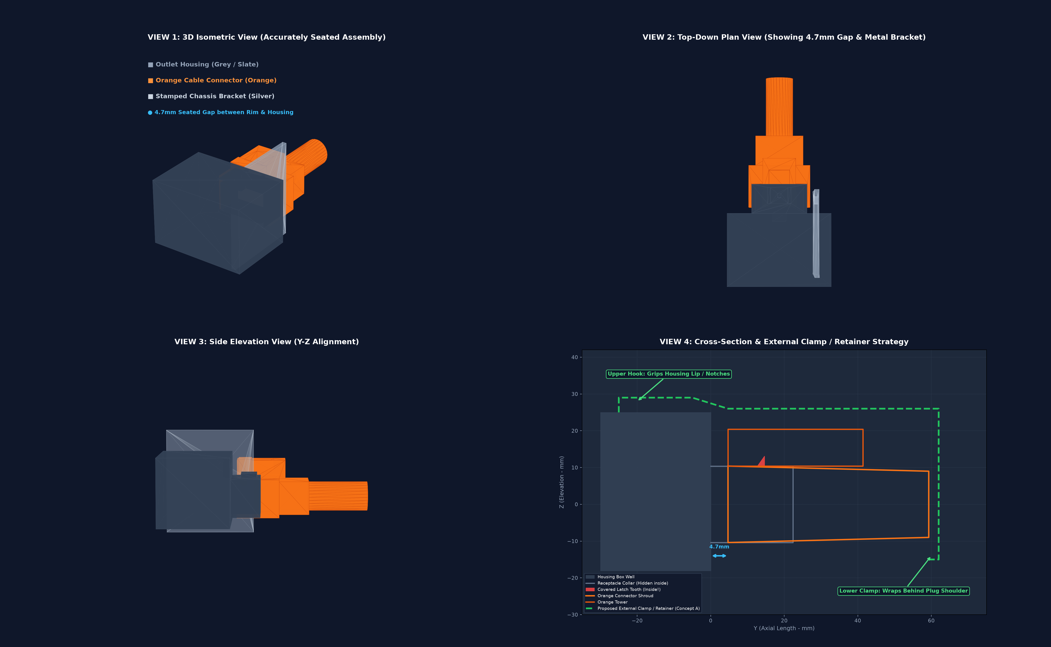
testing/seated_assembly_blueprint.png
