elliotmartin92/hv_lock/accurate_models/measuring_guide_test.png

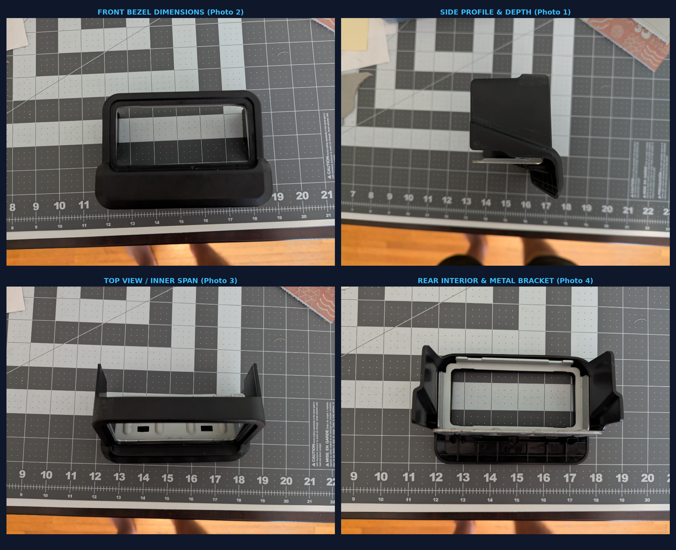
accurate_models/measuring_guide_test.png
