elliotmartin92/hv_lock/testing/c_bracket_blueprint.png

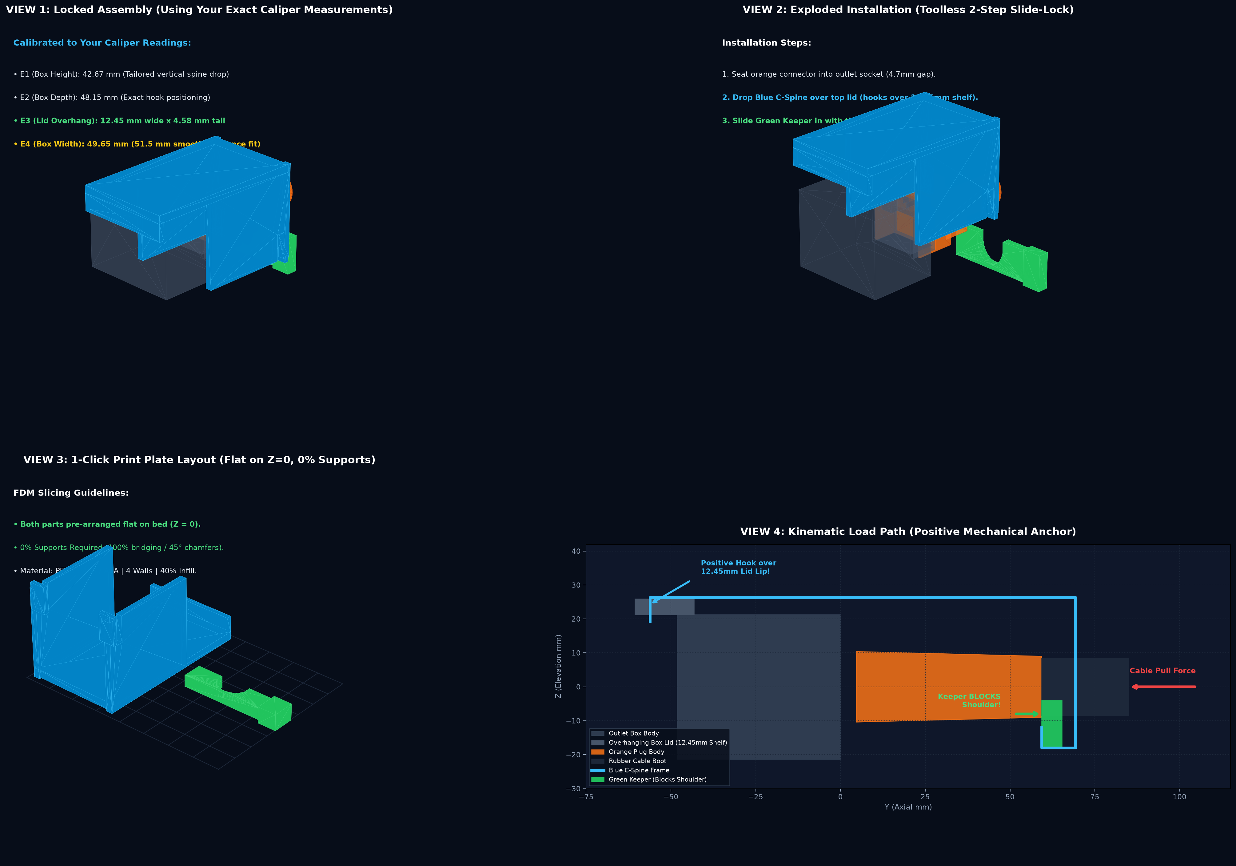
testing/c_bracket_blueprint.png
