elliotmartin92/hv_lock/testing/clear_orthographic_model.png

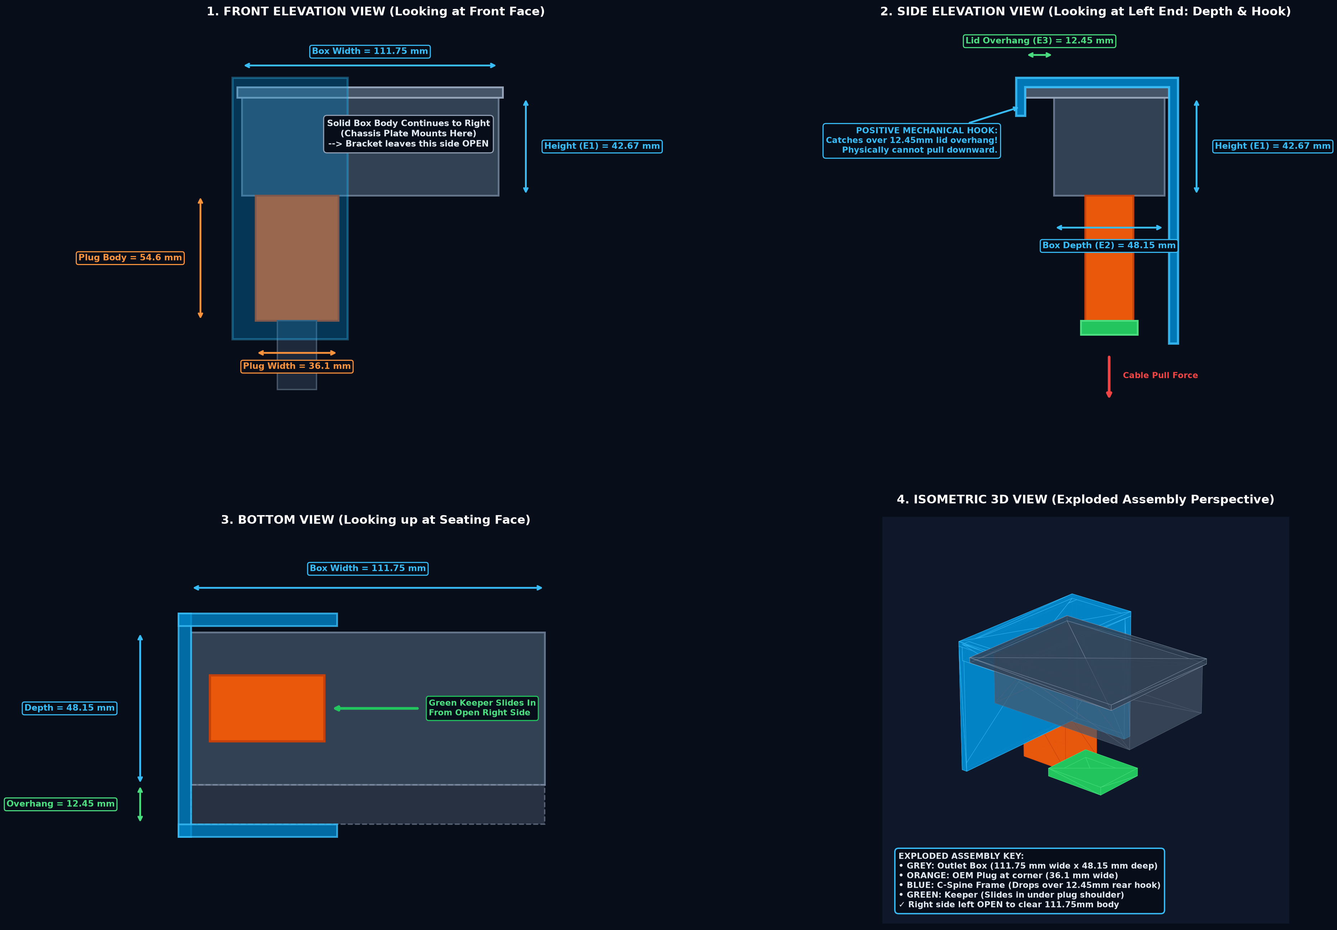
testing/clear_orthographic_model.png
