elliotmartin92/hv_lock/testing/how_it_works_explained.png

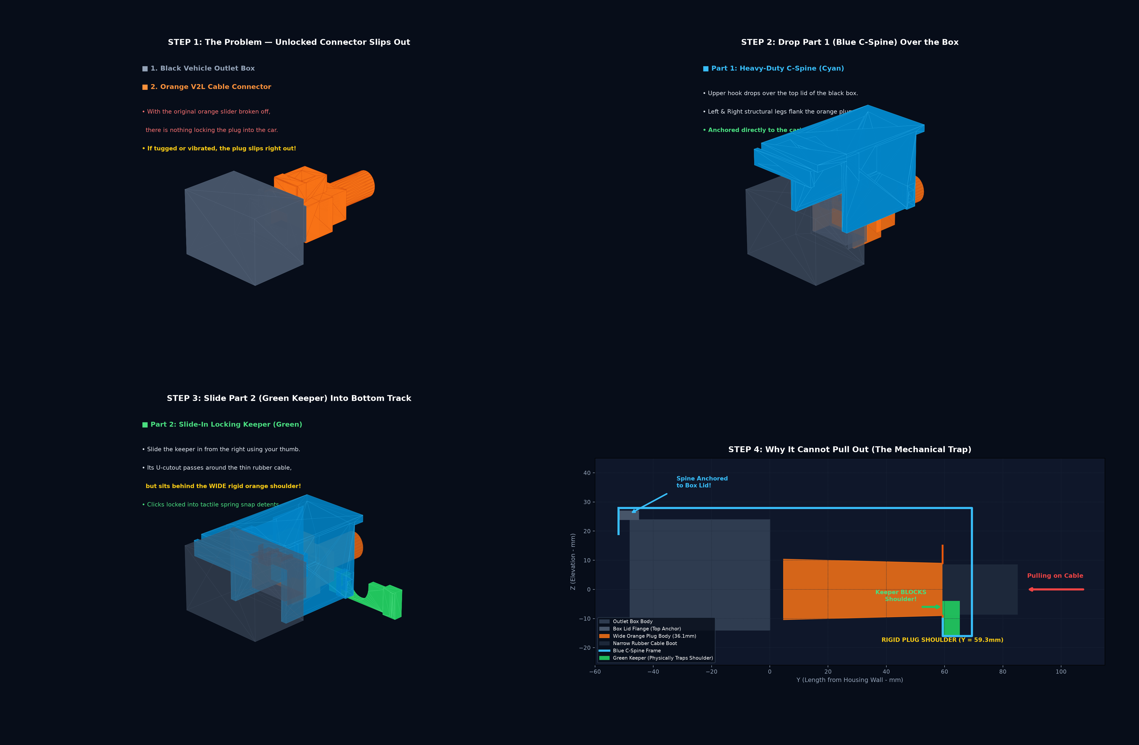
testing/how_it_works_explained.png
