elliotmartin92/hv_lock/testing/hv_lock_blueprint.png

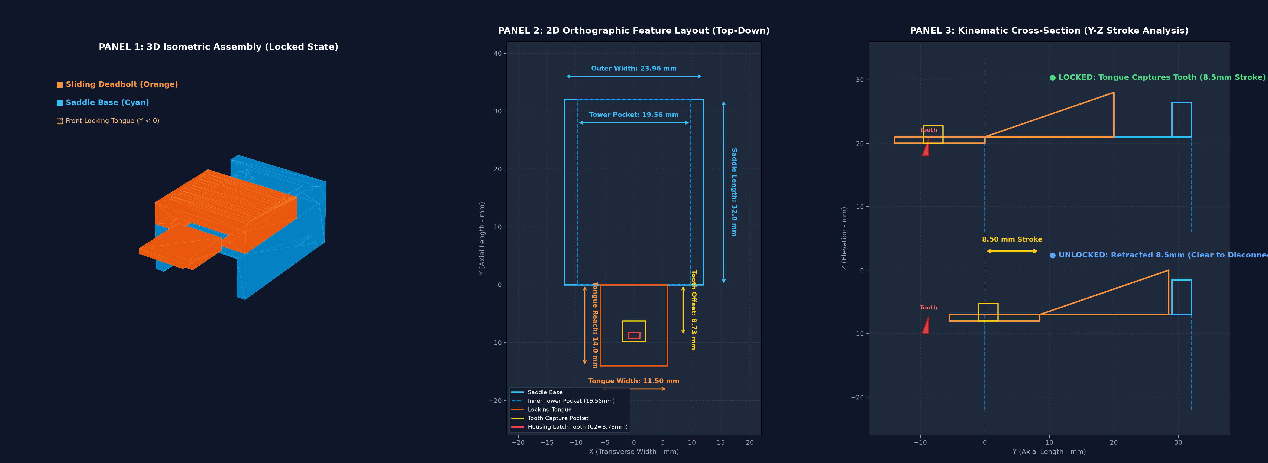
testing/hv_lock_blueprint.png
