elliotmartin92/hv_lock/testing/hv_lock_context_render.png

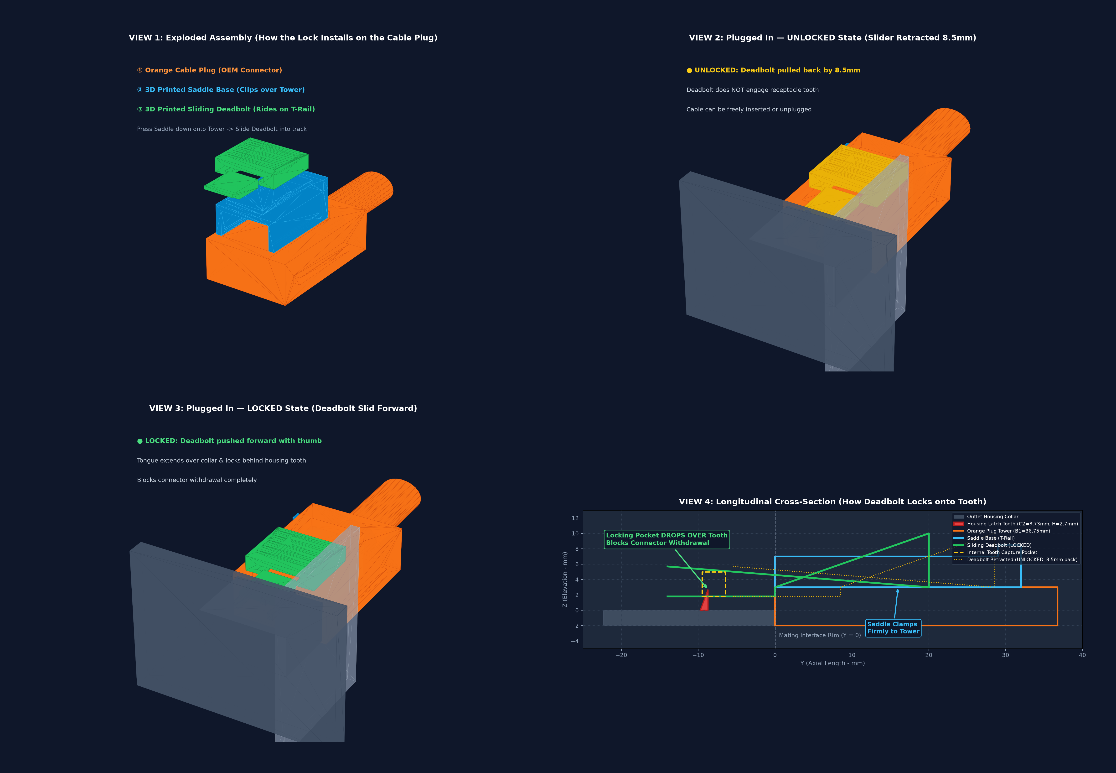
testing/hv_lock_context_render.png
