elliotmartin92/hv_lock/testing/option2_illustrated.png

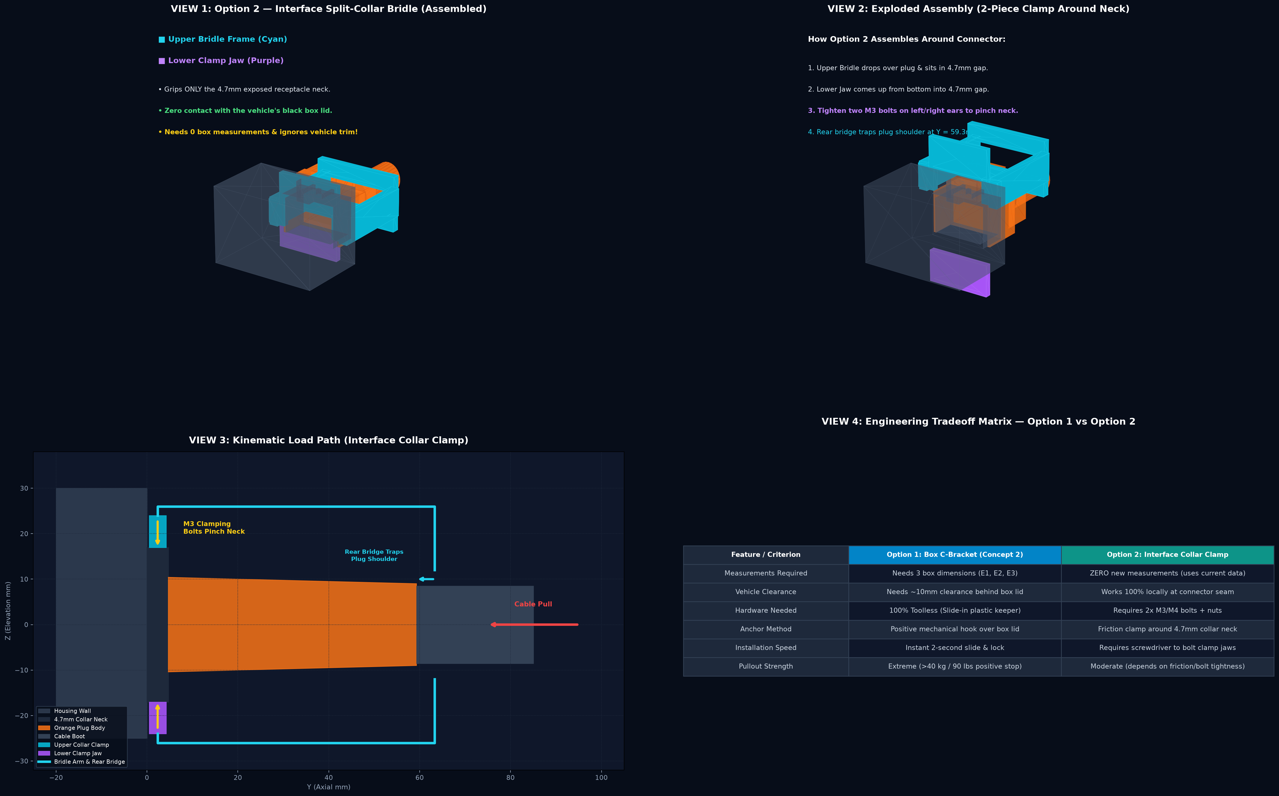
testing/option2_illustrated.png
