elliotmartin92/hv_lock/testing/solution_b_reality.png

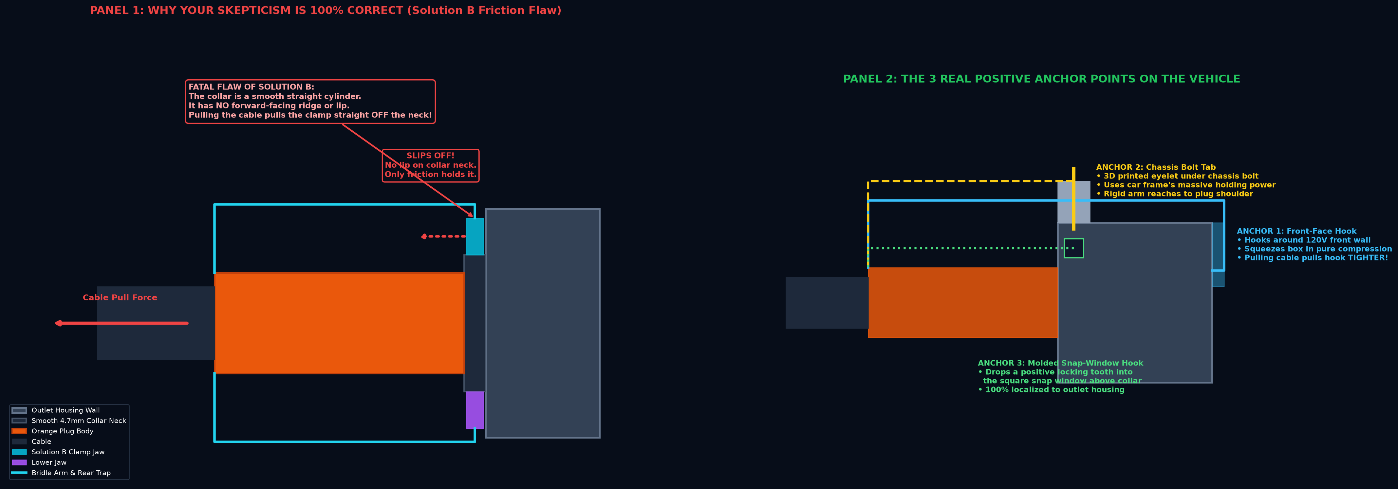
testing/solution_b_reality.png
