elliotmartin92/hv_lock/testing/true_box_orientation.png

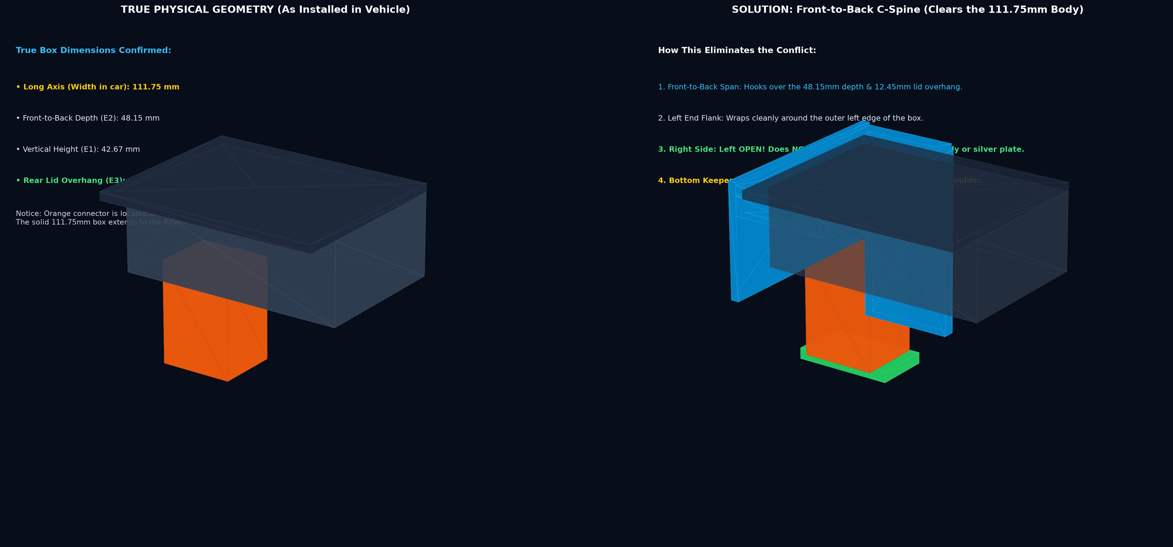
testing/true_box_orientation.png
