elliotmartin92/hv_lock/testing/vehicle_true_orientation.png

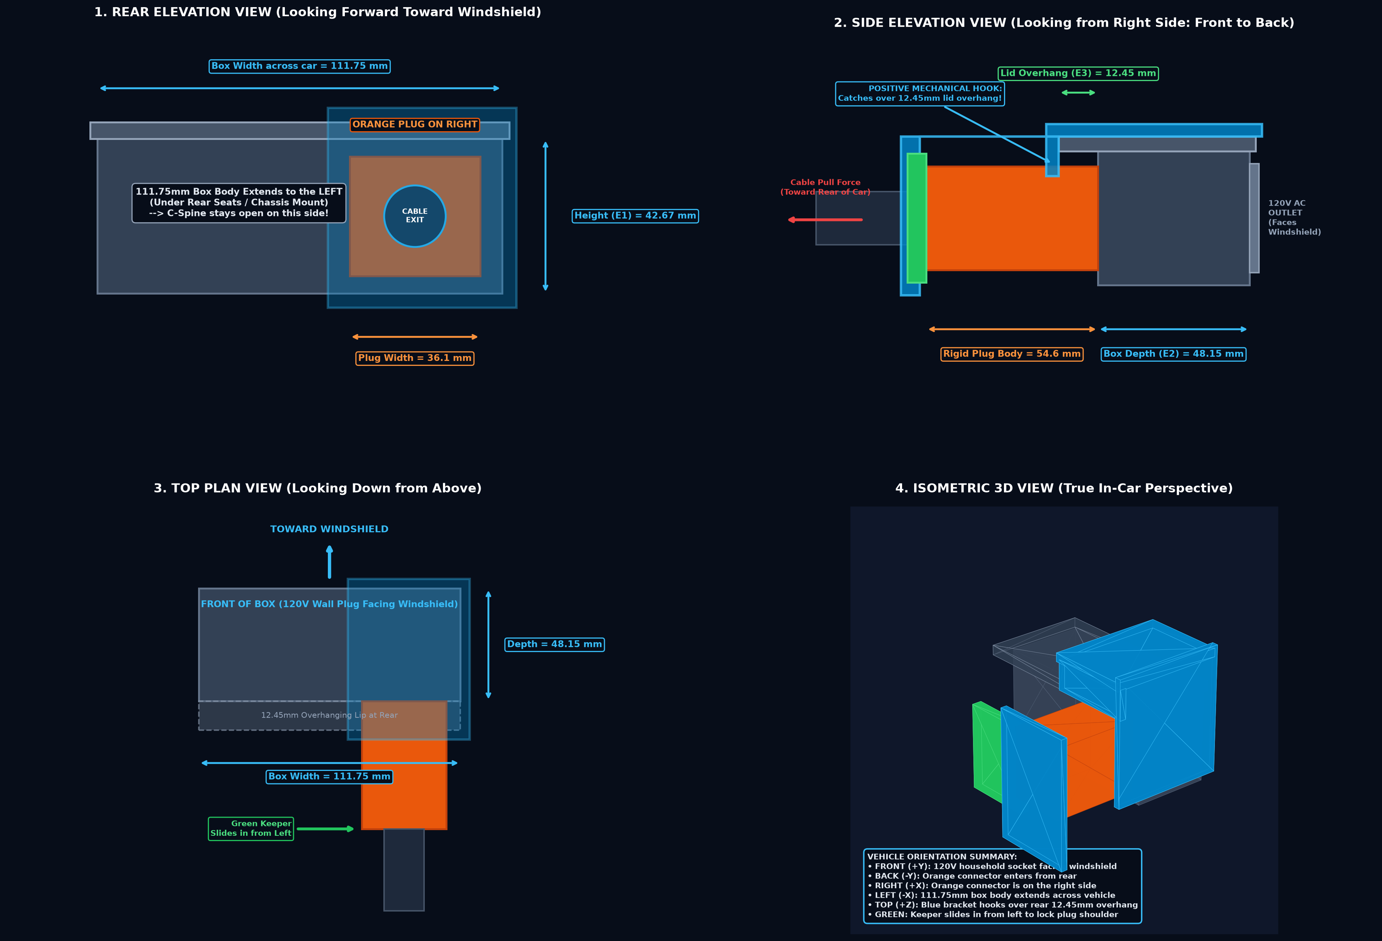
testing/vehicle_true_orientation.png
