elliotmartin92/hv_lock/testing/why_user_is_right.png

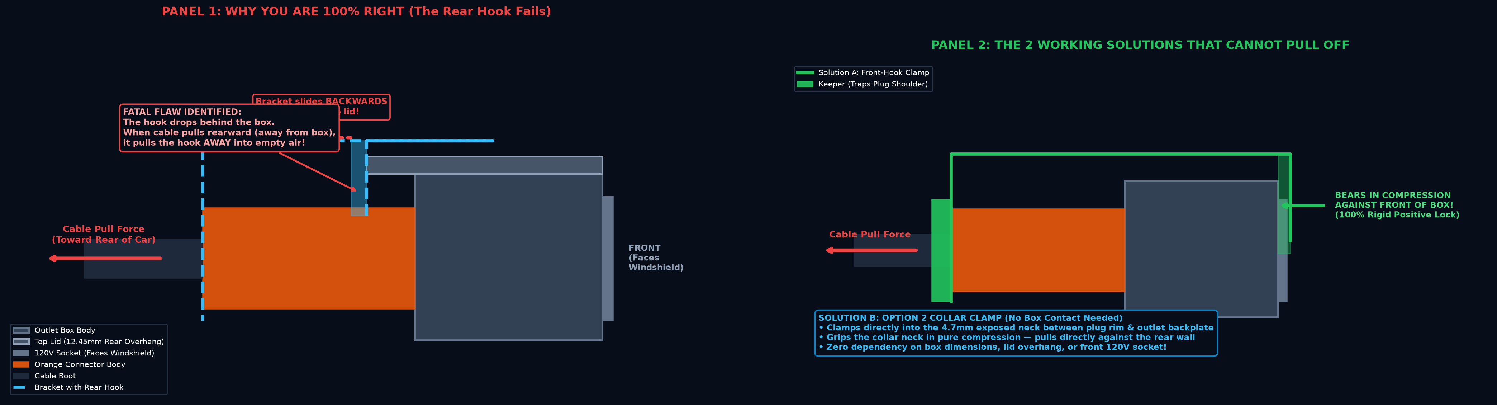
testing/why_user_is_right.png
