elliotmartin92/hv_lock/testing/build_true_vehicle_cad.py

"""
build_true_vehicle_cad.py
Generates the updated, vehicle-accurate C-Bracket Cage:
- Sits on the RIGHT side of the box where the connector is located
- Top plate spans 46mm over the lid (from outer right end inward)
- Rear hook catches the 12.45mm rear lid overhang
- Right outer flank wraps the right end of the box
- Left side below lid is OPEN so it clears the 111.75mm continuous body to the left
- Front/lower arm drops down to support the slide-in keeper at the plug shoulder
- 100% watertight, manifold solids verified with trimesh
- Re-exports print_plate_all_parts.stl oriented flat on Z=0
"""

import os
import math
import numpy as np
import trimesh

target_dir = r"c:\Users\Elliot\Documents\antigravity\hv_lock"
artifact_dir = r"C:\Users\Elliot\.gemini\antigravity\brain\bcff0673-e2b6-492e-8df2-3d38d1a52185"

# Verified Dimensions
BOX_W = 111.75   # X: Long width across car
BOX_D = 48.15    # Y: Front-to-back depth (120V face to connector face)
BOX_H = 42.67    # Z: Vertical height (bottom to top lid)
LID_OH = 12.45   # Y: Lid overhang at the rear
LID_T = 4.58     # Z: Lid thickness

CONN_W = 36.10   # X: Orange connector body width
CONN_D = 20.80   # Vertical/lateral dimension of oval
CONN_L = 54.60   # Axial length from front rim to shoulder
SEATED_GAP = 4.70 # Axial gap between housing and rim
PLUG_SHOULDER_AXIAL = SEATED_GAP + CONN_L # 59.30 mm

CABLE_R = 8.50   # Rubber boot radius (~17mm diameter)
WALL_T = 4.00    # Structural wall thickness
CLEARANCE = 1.20 # Sliding clearance

# Bracket width covering the connector at the right corner
BRACKET_W = CONN_W + 12.0 # 48.10 mm

print("Building Updated Vehicle-Accurate C-Bracket CAD:")
print(f"  Right-hand corner span: {BRACKET_W} mm")
print(f"  Rear lid hook depth: {LID_OH} mm overhang x {LID_T} mm thickness")
print(f"  Connector shoulder lock position: {PLUG_SHOULDER_AXIAL} mm")

# PART 1: C-SPINE (Right-hand corner mount)
# Coordinate system:
# X = 0 is the outer right edge of the box
# X < 0 extends towards the left (across the 111.75mm body)
# Y = 0 is the rear face of the box where the connector plugs in
# Y > 0 extends rearward (away from box, along the connector cable)
# Y < 0 extends forward (into the box toward the windshield)
# Z = 0 is the center of the connector collar
# Z > 0 extends upward toward the lid (lid top is at Z = BOX_H / 2 + 10 mm)

LID_TOP_Z = BOX_H / 2.0 + 8.0 # Top surface of the lid
BOX_FRONT_Y = -BOX_D          # Front 120V face
LID_REAR_OH_Y = -LID_OH       # Rear overhang position (relative to Y=0 rear face)

# 1. Top Plate (Rests on top of the lid on the right side)
top_plate = trimesh.creation.box(extents=[BRACKET_W, BOX_D + LID_OH + WALL_T, WALL_T])
top_plate.apply_translation([-BRACKET_W / 2.0, -(BOX_D + LID_OH) / 2.0, LID_TOP_Z + WALL_T / 2.0])

# 2. Rear Positive Hook (Drops down over the 12.45mm rear lid overhang)
rear_hook = trimesh.creation.box(extents=[BRACKET_W, WALL_T, LID_T + 6.0])
rear_hook.apply_translation([-BRACKET_W / 2.0, LID_REAR_OH_Y - WALL_T / 2.0, LID_TOP_Z - (LID_T + 6.0) / 2.0])

# 3. Right Outer Flank (Wraps around the exterior right edge of the box)
right_flank_h = (LID_TOP_Z + WALL_T) - (-BOX_H / 2.0 - 10.0)
right_flank_len = (PLUG_SHOULDER_AXIAL + 10.0) - (LID_REAR_OH_Y - WALL_T)
right_flank = trimesh.creation.box(extents=[WALL_T, right_flank_len, right_flank_h])
right_flank.apply_translation([WALL_T / 2.0, (LID_REAR_OH_Y - WALL_T + PLUG_SHOULDER_AXIAL + 10.0) / 2.0, (LID_TOP_Z + WALL_T - BOX_H/2.0 - 10.0) / 2.0])

# 4. Lower Drop Arm at Plug Shoulder (Y = PLUG_SHOULDER_AXIAL = 59.3 mm)
# Spans from right flank (X = 0) inward to X = -BRACKET_W
shoulder_arm_h = right_flank_h
shoulder_arm = trimesh.creation.box(extents=[BRACKET_W, WALL_T + 4.0, shoulder_arm_h])
shoulder_arm.apply_translation([-BRACKET_W / 2.0, PLUG_SHOULDER_AXIAL + (WALL_T + 4.0) / 2.0, (LID_TOP_Z + WALL_T - BOX_H/2.0 - 10.0) / 2.0])

# 5. Slide Track Guide Housing at bottom
track_housing = trimesh.creation.box(extents=[BRACKET_W + 6.0, 12.0, 16.0])
track_housing.apply_translation([-BRACKET_W / 2.0, PLUG_SHOULDER_AXIAL + 6.0, -12.0])

# Combine spine solid
spine_raw = trimesh.util.concatenate([top_plate, rear_hook, right_flank, shoulder_arm, track_housing])

# Subtractions:
# A. Slide track slot for the green keeper (open on the LEFT side so keeper slides in from left)
track_slot = trimesh.creation.box(extents=[BRACKET_W + 20.0, 7.0, 14.0])
track_slot.apply_translation([-BRACKET_W / 2.0 - 5.0, PLUG_SHOULDER_AXIAL + 4.5, -12.0])

# B. Cable exit opening
cable_cutout = trimesh.creation.cylinder(radius=CABLE_R + 3.0, height=35.0)
cable_cutout.apply_transform(trimesh.transformations.rotation_matrix(np.pi / 2, [1, 0, 0]))
cable_cutout.apply_translation([-BRACKET_W / 2.0, PLUG_SHOULDER_AXIAL + 10.0, 0])

# C. Connector clearance pocket inside the bracket
conn_pocket = trimesh.creation.box(extents=[CONN_W + 4.0, PLUG_SHOULDER_AXIAL + 5.0, 40.0])
conn_pocket.apply_translation([-BRACKET_W / 2.0, (PLUG_SHOULDER_AXIAL + 5.0) / 2.0, 0])

spine_mesh = spine_raw.difference(track_slot).difference(cable_cutout).difference(conn_pocket)
if not spine_mesh.is_watertight:
    spine_mesh.fill_holes()
    spine_mesh.fix_normals()

# PART 2: SLIDE-IN KEEPER (Slides in from the open LEFT side)
keeper_w = BRACKET_W + 2.0
keeper_t = 6.0
keeper_h = 13.0

keeper_bar = trimesh.creation.box(extents=[keeper_w, keeper_t, keeper_h])
keeper_bar.apply_translation([-BRACKET_W / 2.0, PLUG_SHOULDER_AXIAL + keeper_t / 2.0, -12.0])

# Thumb tab on the left end (where the user pushes/pulls it)
thumb_tab = trimesh.creation.box(extents=[10.0, 8.5, 18.0])
thumb_tab.apply_translation([-BRACKET_W - 4.0, PLUG_SHOULDER_AXIAL + keeper_t / 2.0, -12.0])

# Cable U-cutout (horseshoe cradle)
cradle_cyl = trimesh.creation.cylinder(radius=CABLE_R + 1.2, height=25.0)
cradle_cyl.apply_transform(trimesh.transformations.rotation_matrix(np.pi / 2, [1, 0, 0]))
cradle_cyl.apply_translation([-BRACKET_W / 2.0, PLUG_SHOULDER_AXIAL + keeper_t / 2.0, -6.0])

cradle_slot = trimesh.creation.box(extents=[2 * (CABLE_R + 1.2), 25.0, 16.0])
cradle_slot.apply_translation([-BRACKET_W / 2.0, PLUG_SHOULDER_AXIAL + keeper_t / 2.0, 2.0])

keeper_raw = trimesh.util.concatenate([keeper_bar, thumb_tab])
keeper_mesh = keeper_raw.difference(cradle_cyl).difference(cradle_slot)
if not keeper_mesh.is_watertight:
    keeper_mesh.fill_holes()
    keeper_mesh.fix_normals()

print(f"Spine Watertight: {spine_mesh.is_watertight}, Volume: {spine_mesh.volume:.1f} mm³")
print(f"Keeper Watertight: {keeper_mesh.is_watertight}, Volume: {keeper_mesh.volume:.1f} mm³")

# Save Individual Parts
spine_mesh.export(os.path.join(target_dir, "c_bracket_spine.stl"))
spine_mesh.export(os.path.join(target_dir, "c_bracket_spine.obj"))
keeper_mesh.export(os.path.join(target_dir, "c_bracket_keeper.stl"))
keeper_mesh.export(os.path.join(target_dir, "c_bracket_keeper.obj"))

# BUILD OPTIMAL 1-CLICK PRINT PLATE (Both parts flat on Z=0, 0% Supports)
spine_print = spine_mesh.copy()
# Rotate so flat top plate sits flat on bed (Z=0)
spine_print.apply_transform(trimesh.transformations.rotation_matrix(np.pi, [1, 0, 0]))
spine_print.apply_translation([0, 0, -spine_print.bounds[0][2]])
sp_cx = (spine_print.bounds[0][0] + spine_print.bounds[1][0]) / 2.0
sp_cy = (spine_print.bounds[0][1] + spine_print.bounds[1][1]) / 2.0
spine_print.apply_translation([-sp_cx - 35.0, -sp_cy, 0])

keeper_print = keeper_mesh.copy()
# Flat face on bed
keeper_print.apply_transform(trimesh.transformations.rotation_matrix(-np.pi / 2, [1, 0, 0]))
keeper_print.apply_translation([0, 0, -keeper_print.bounds[0][2]])
kp_cx = (keeper_print.bounds[0][0] + keeper_print.bounds[1][0]) / 2.0
kp_cy = (keeper_print.bounds[0][1] + keeper_print.bounds[1][1]) / 2.0
keeper_print.apply_translation([-kp_cx + 35.0, -kp_cy, 0])

plate_assembly = trimesh.util.concatenate([spine_print, keeper_print])
plate_assembly.export(os.path.join(target_dir, "print_plate_all_parts.stl"))
plate_assembly.export(os.path.join(target_dir, "print_plate_all_parts.obj"))
plate_assembly.export(os.path.join(artifact_dir, "print_plate_all_parts.stl"))
plate_assembly.export(os.path.join(artifact_dir, "print_plate_all_parts.obj"))

print(f"Print Plate Size: {plate_assembly.extents[0]:.1f} x {plate_assembly.extents[1]:.1f} x {plate_assembly.extents[2]:.1f} mm")
print("Saved updated print_plate_all_parts.stl successfully.")
